IvanCanedo/Re-configurableDrivingSimulatorPrototype/Solidworks/Full-Scale/plataforma.SLDASM

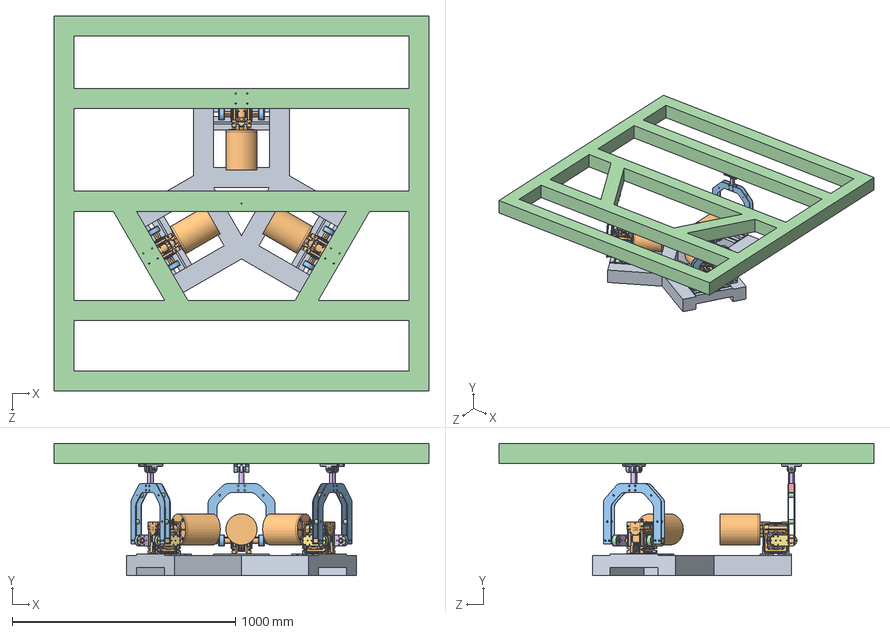
[picture p16: CAD file, 2021-12-05]
Solidworks/Full-Scale/plataforma.SLDASM
1680.0 x 593.5 x 1680.0 mm
base
reductor con motor x 3
cople flecha x 6
cople rodamiento x 6
rodameitno falso x 6
placa manivela x 6
placa manivela 2 x 6
tornillo falso x 72
anillo manivela x 6
pin de manivela x 6
arco x 6
virlo x 12
bloque x 3
rotula x 3
esfera x 3
placa superior x 3
soporte superior x 6
pin superior x 3
virlo superior x 6
base superior
