IvanCanedo/Re-configurableDrivingSimulatorPrototype/Solidworks/Scale/Ensamblaje1.SLDASM

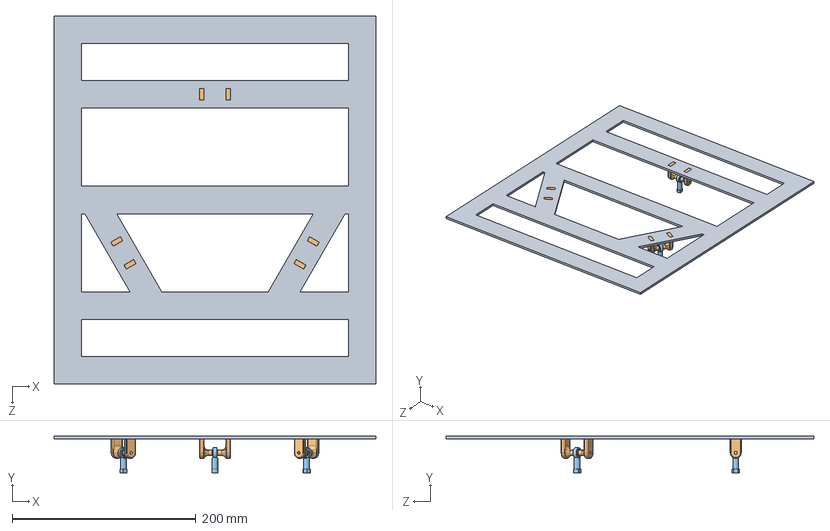
[picture p17: CAD file, 2021-12-05]
Solidworks/Scale/Ensamblaje1.SLDASM
350.0 x 39.7 x 400.0 mm
plataforma superior
soporte superior x 6
rotula de esfera x 3
