IvanCanedo/Re-configurableDrivingSimulatorPrototype/Solidworks/Vehicle control devices/pedalEnsable.SLDASM

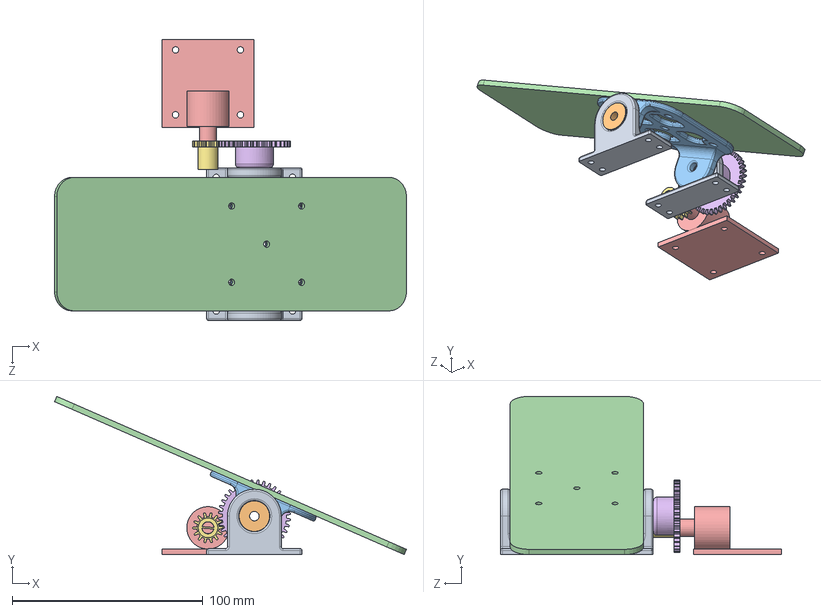
[picture p18: CAD file, 2021-12-05]
Solidworks/Vehicle control devices/pedalEnsable.SLDASM
184.4 x 82.9 x 147.2 mm
abrazadera5-16 x 2
rodamiento5-16 x 2
base pedal
pedal
pot
gear36
gear14
