IvanCanedo/Re-configurableDrivingSimulatorPrototype/Solidworks/Full-Scale/plataforma con perfiles y tornillos.SLDASM

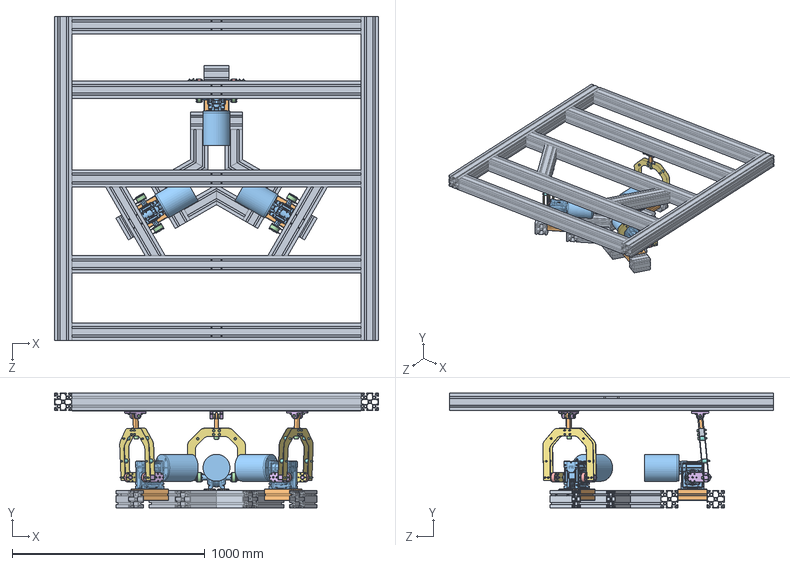
[picture p19: CAD file, 2021-12-05]
Solidworks/Full-Scale/plataforma con perfiles y tornillos.SLDASM
1680.0 x 594.1 x 1680.0 mm
perfil extruido 90x90 x 21
perfil extruido 60x60 x 6
reductor con motor x 3
cople flecha x 6
cople rodamiento x 6
placa manivela 2 x 6
placa manivela x 6
2202_ETN9_3 x 60
2202_ETN9_14 x 60
2202_ETN9_29 x 6
2202_ETN9_31 x 6
socket head cap screw_iso x 129
anillo manivela x 6
pin de manivela x 6
arco x 6
virlo x 12
bloque x 3
rotula x 3
esfera x 3
pin superior x 3
placa superior x 3
soporte superior x 6
virlo superior x 6
