IvanCanedo/Re-configurableDrivingSimulatorPrototype/Solidworks/Full-Scale/soperte superior.SLDASM

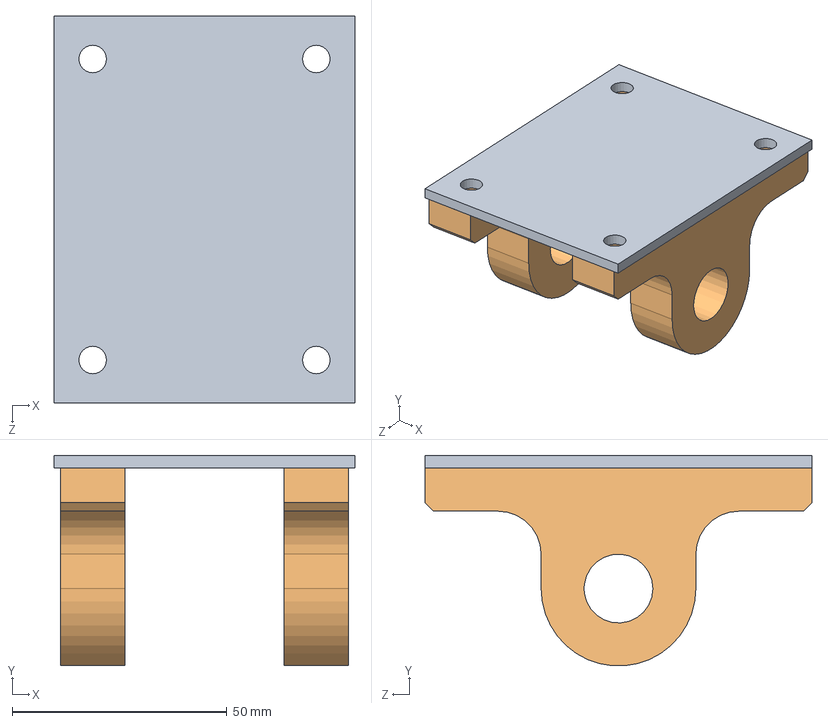
[picture p20: CAD file, 2021-12-05]
Solidworks/Full-Scale/soperte superior.SLDASM
70.0 x 48.9 x 90.0 mm
placa superior
soporte superior x 2
