IvanCanedo/Re-configurableDrivingSimulatorPrototype/Solidworks/Full-Scale/manivela con rodamiento derecha.SLDASM

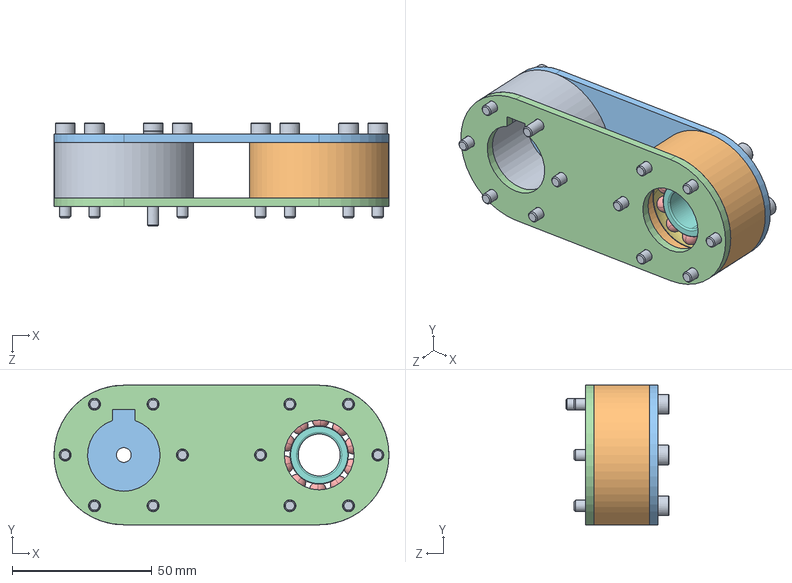
[picture p21: CAD file, 2021-12-05]
Solidworks/Full-Scale/manivela con rodamiento derecha.SLDASM
120.0 x 50.0 x 37.0 mm
cople flecha
cople rodamiento
placa manivela 2
placa manivela
2202_ETN9_3 x 10
2202_ETN9_14 x 10
2202_ETN9_29
2202_ETN9_31
socket head cap screw_iso x 12
anillo manivela
