IvanCanedo/Re-configurableDrivingSimulatorPrototype/Solidworks/Full-Scale/base superior con perfiles.SLDASM

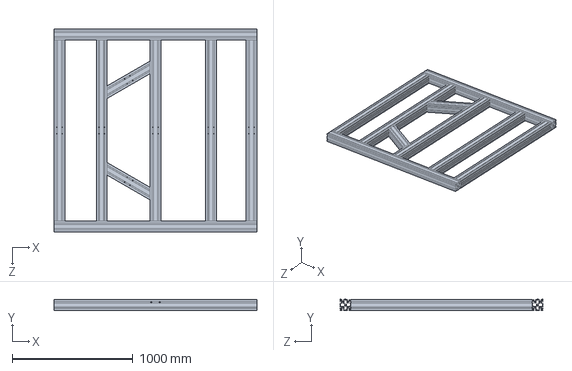
[picture p22: CAD file, 2021-12-05]
Solidworks/Full-Scale/base superior con perfiles.SLDASM
1680.0 x 92.0 x 1680.0 mm
perfil extruido 90x90 x 9
