IvanCanedo/Re-configurableDrivingSimulatorPrototype/Solidworks/Full-Scale/arco ensamble.SLDASM

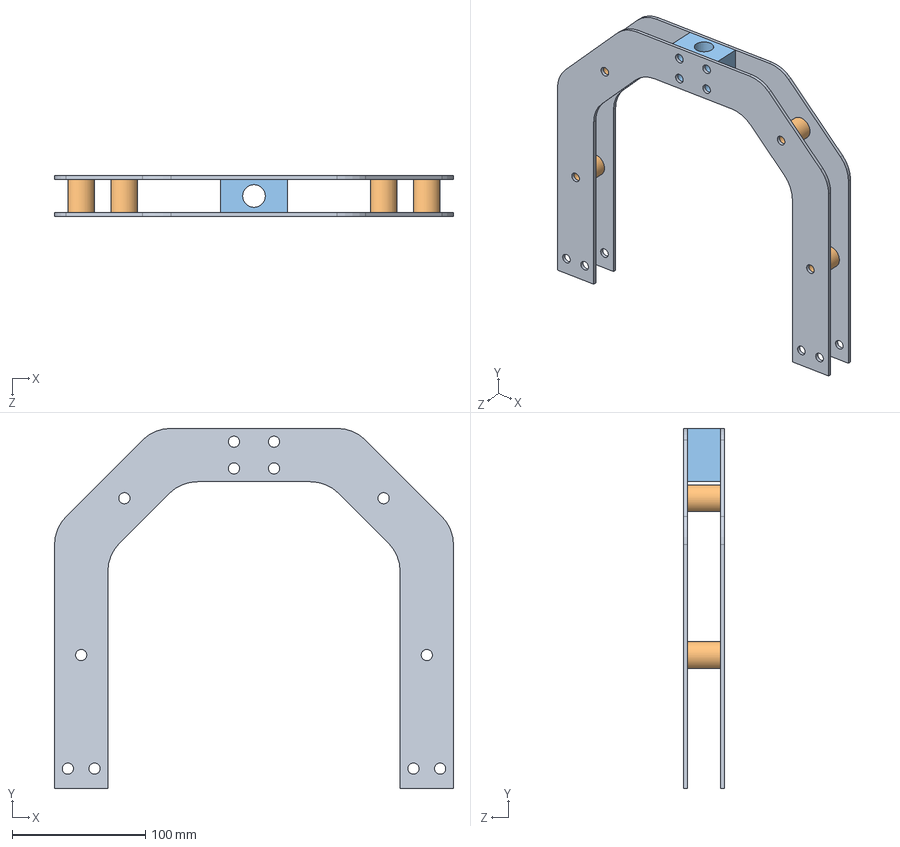
[picture p23: CAD file, 2021-12-05]
Solidworks/Full-Scale/arco ensamble.SLDASM
299.0 x 270.0 x 31.0 mm
arco x 2
virlo x 4
bloque
