IvanCanedo/Re-configurableDrivingSimulatorPrototype/MATLAB/simulacion/pilar.SLDPRT

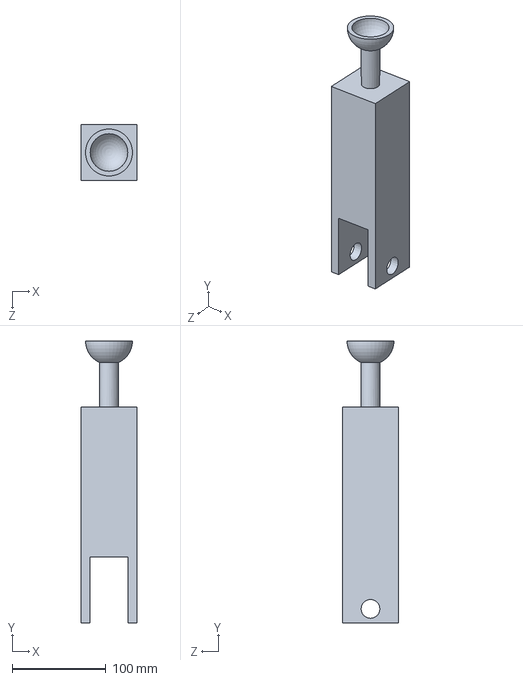
[picture p24: CAD file, 2021-12-05]
MATLAB/simulacion/pilar.SLDPRT
60.0 x 300.0 x 60.0 mm
