IvanCanedo/Re-configurableDrivingSimulatorPrototype/Solidworks/Finite Element/flecha motor.SLDPRT

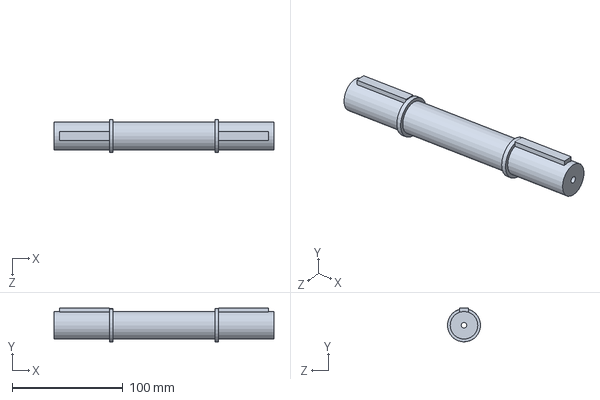
[picture p25: CAD file, 2021-12-05]
Solidworks/Finite Element/flecha motor.SLDPRT
199.0 x 30.5 x 30.0 mm
