IvanCanedo/Re-configurableDrivingSimulatorPrototype/Solidworks/Full-Scale/diagrama base.SLDPRT

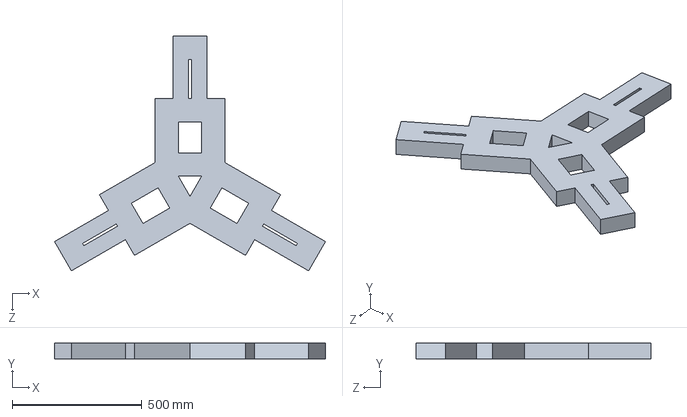
[picture p26: CAD file, 2021-12-05]
Solidworks/Full-Scale/diagrama base.SLDPRT
1043.6 x 60.0 x 903.8 mm
