IvanCanedo/Re-configurableDrivingSimulatorPrototype/Solidworks/Scale/soporte silla.SLDPRT

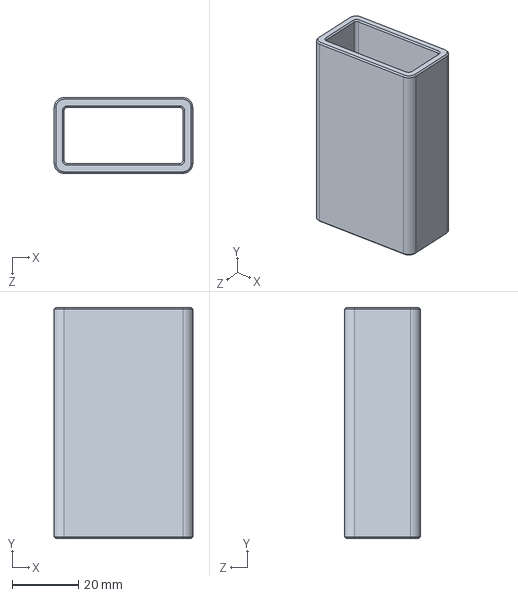
[picture p27: CAD file, 2021-12-05]
Solidworks/Scale/soporte silla.SLDPRT
42.0 x 70.0 x 23.0 mm
