IvanCanedo/Re-configurableDrivingSimulatorPrototype/Solidworks/Vehicle control devices/cople volante.SLDPRT

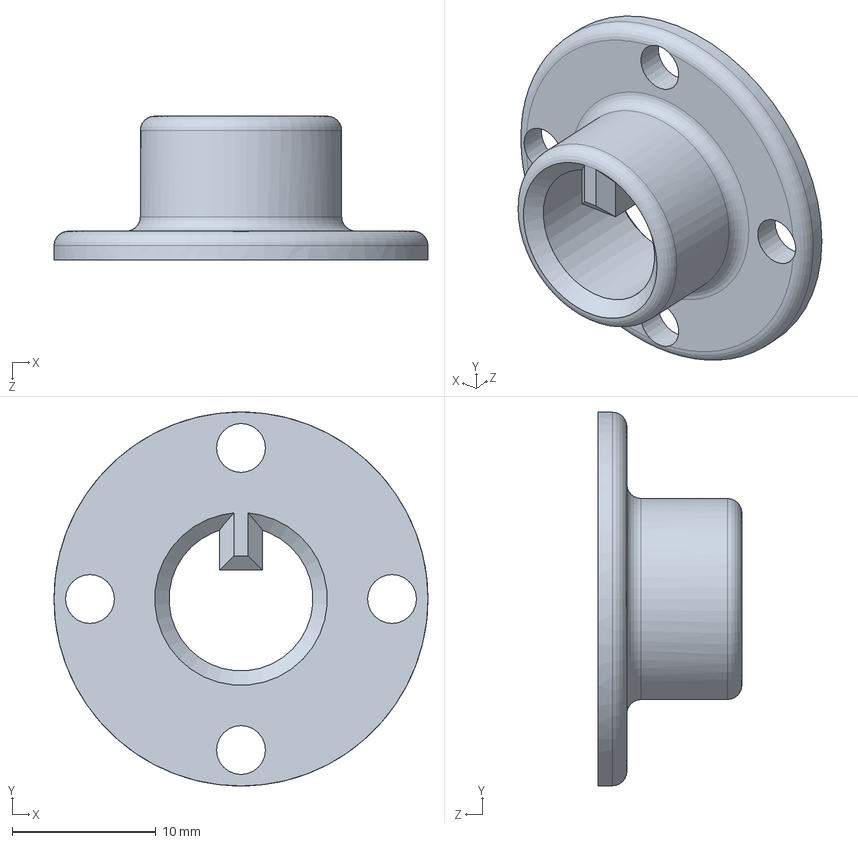
[picture p28: CAD file, 2021-12-05]
Solidworks/Vehicle control devices/cople volante.SLDPRT
26.0 x 26.0 x 10.0 mm
