IvanCanedo/Re-configurableDrivingSimulatorPrototype/Solidworks/Finite Element/bloque.SLDPRT

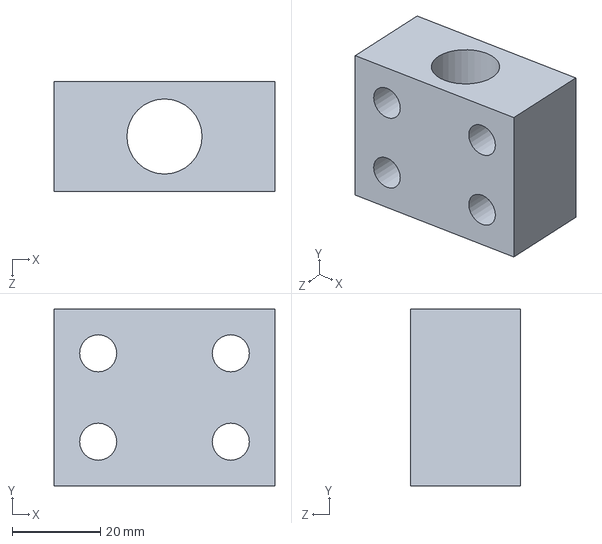
[picture p29: CAD file, 2021-12-05]
Solidworks/Finite Element/bloque.SLDPRT
50.0 x 40.0 x 25.0 mm
