IvanCanedo/Re-configurableDrivingSimulatorPrototype/Solidworks/Full-Scale/cople rodamiento.SLDPRT

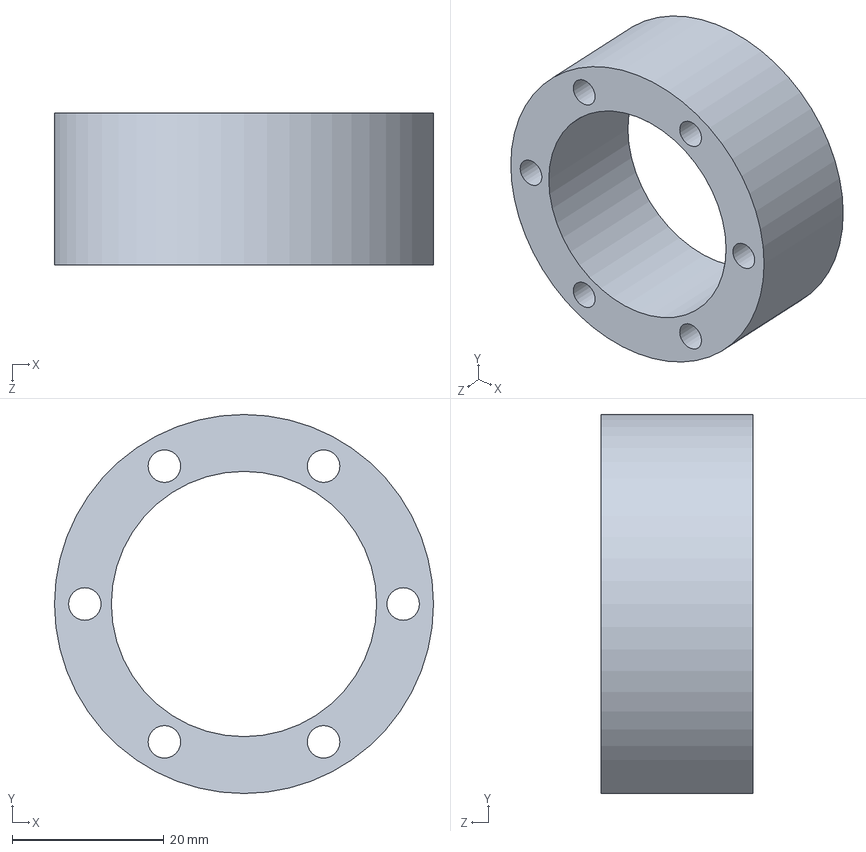
[picture p30: CAD file, 2021-12-05]
Solidworks/Full-Scale/cople rodamiento.SLDPRT
50.0 x 50.0 x 20.0 mm
