IvanCanedo/Re-configurableDrivingSimulatorPrototype/Solidworks/Scale/base plataforma.SLDPRT

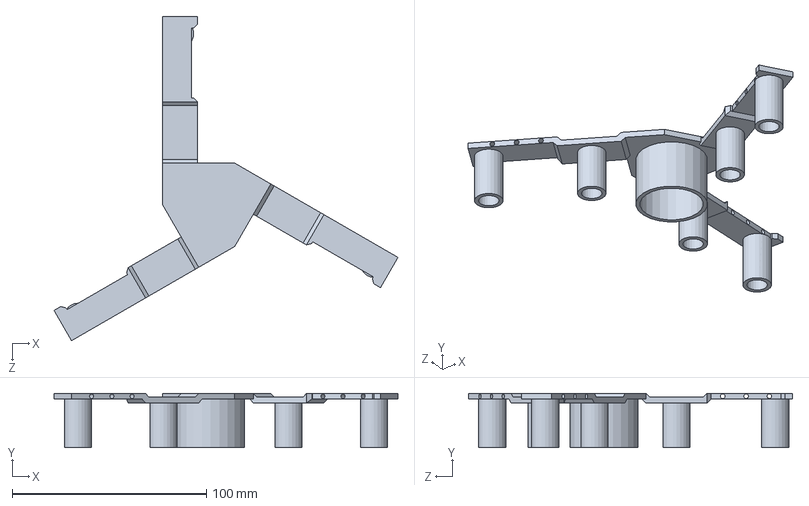
[picture p31: CAD file, 2021-12-05]
Solidworks/Scale/base plataforma.SLDPRT
177.0 x 28.0 x 166.9 mm
