IvanCanedo/Re-configurableDrivingSimulatorPrototype/MATLAB/simulacion/plataforma_Predeterminado_sldprt.STEP

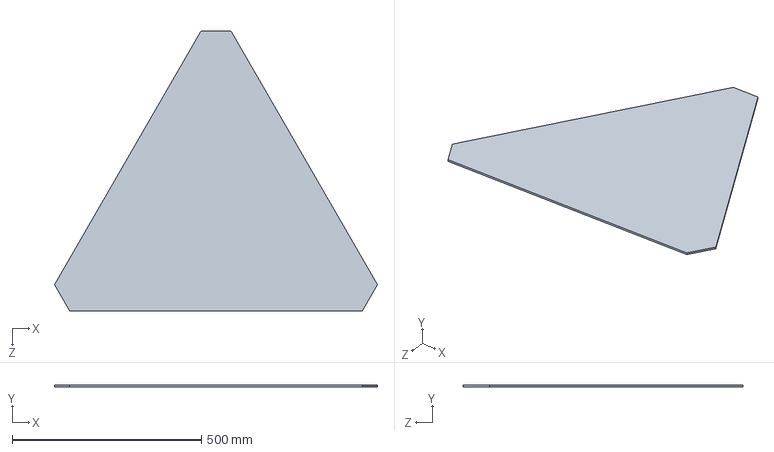
[picture p32: CAD file, 2021-12-05]
MATLAB/simulacion/plataforma_Predeterminado_sldprt.STEP
854.1 x 5.00 x 739.6 mm
