IvanCanedo/Re-configurableDrivingSimulatorPrototype/Solidworks/Finite Element/arco.SLDPRT

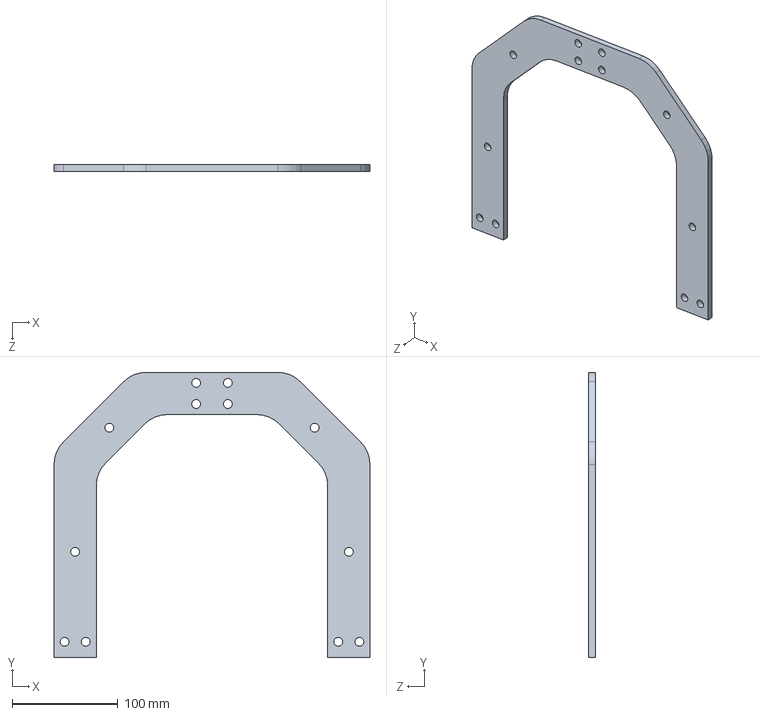
[picture p33: CAD file, 2021-12-05]
Solidworks/Finite Element/arco.SLDPRT
299.0 x 270.0 x 6.35 mm
