IvanCanedo/Re-configurableDrivingSimulatorPrototype/Solidworks/Full-Scale/cople flecha.SLDPRT

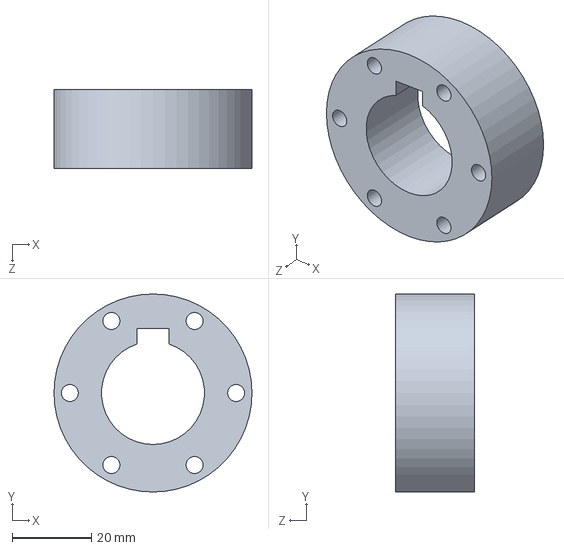
[picture p34: CAD file, 2021-12-05]
Solidworks/Full-Scale/cople flecha.SLDPRT
50.0 x 50.0 x 20.0 mm
