IvanCanedo/Re-configurableDrivingSimulatorPrototype/Solidworks/Scale/soporte superior.SLDPRT

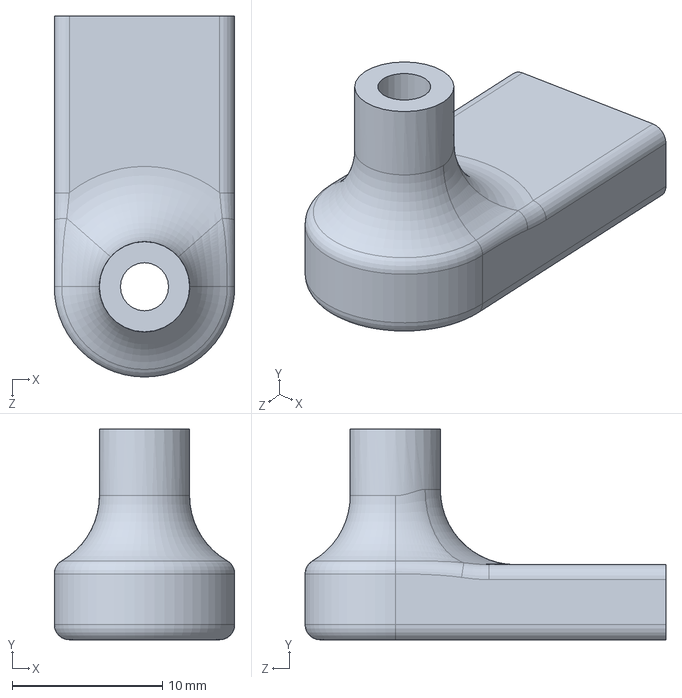
[picture p35: CAD file, 2021-12-05]
Solidworks/Scale/soporte superior.SLDPRT
12.0 x 14.0 x 24.0 mm
