IvanCanedo/Re-configurableDrivingSimulatorPrototype/Solidworks/Vehicle control devices/tapa rodamiento.SLDPRT

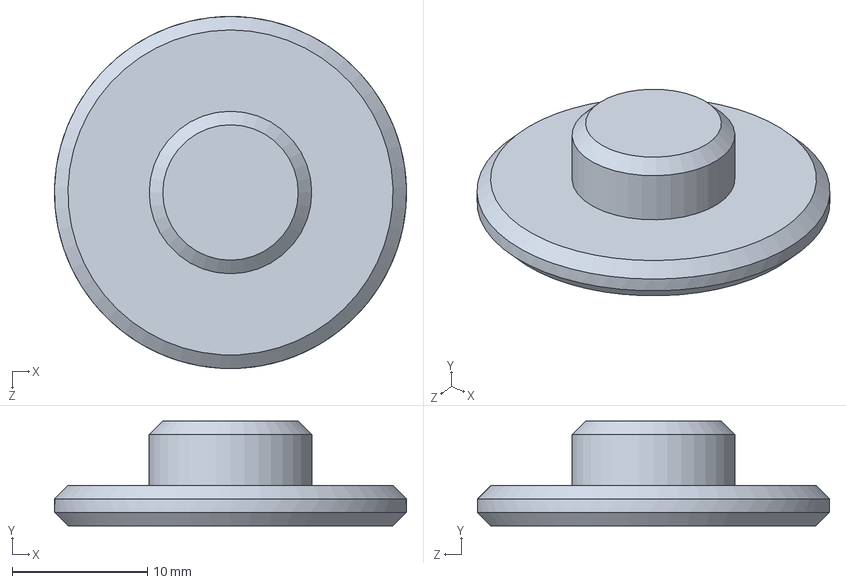
[picture p36: CAD file, 2021-12-05]
Solidworks/Vehicle control devices/tapa rodamiento.SLDPRT
26.0 x 7.75 x 26.0 mm
