IvanCanedo/Re-configurableDrivingSimulatorPrototype/MATLAB/simulacion/plataforma_soporte_Predeterminado_sldprt.STEP

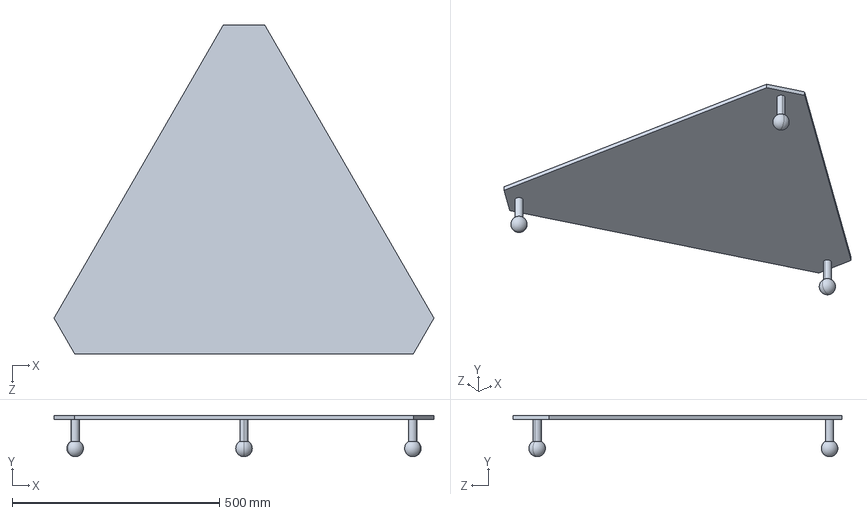
[picture p37: CAD file, 2021-12-05]
MATLAB/simulacion/plataforma_soporte_Predeterminado_sldprt.STEP
916.0 x 100.0 x 793.3 mm
