IvanCanedo/Re-configurableDrivingSimulatorPrototype/Solidworks/Finite Element/esfera.SLDPRT

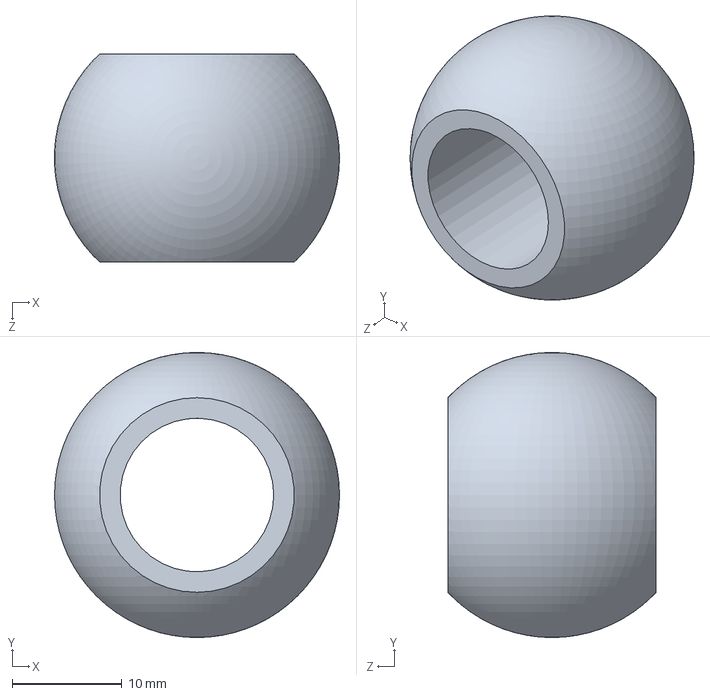
[picture p38: CAD file, 2021-12-05]
Solidworks/Finite Element/esfera.SLDPRT
26.0 x 26.0 x 19.0 mm
