IvanCanedo/Re-configurableDrivingSimulatorPrototype/Solidworks/Scale/rodamiento.SLDPRT

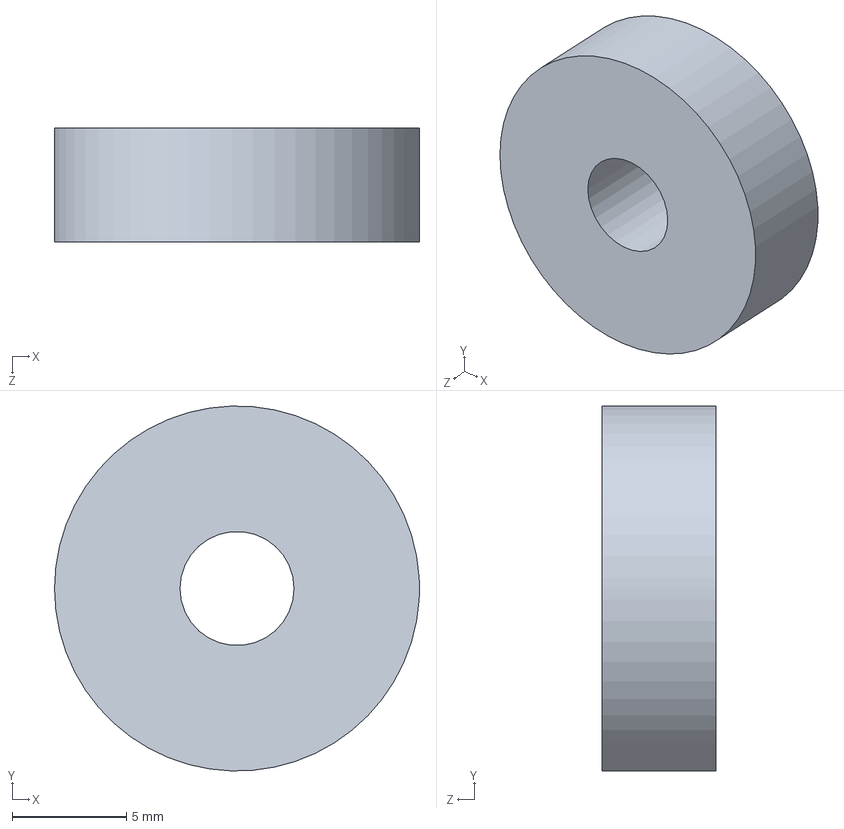
[picture p39: CAD file, 2021-12-05]
Solidworks/Scale/rodamiento.SLDPRT
16.0 x 16.0 x 5.00 mm
