IvanCanedo/Re-configurableDrivingSimulatorPrototype/Solidworks/Vehicle control devices/rodamiento.SLDPRT

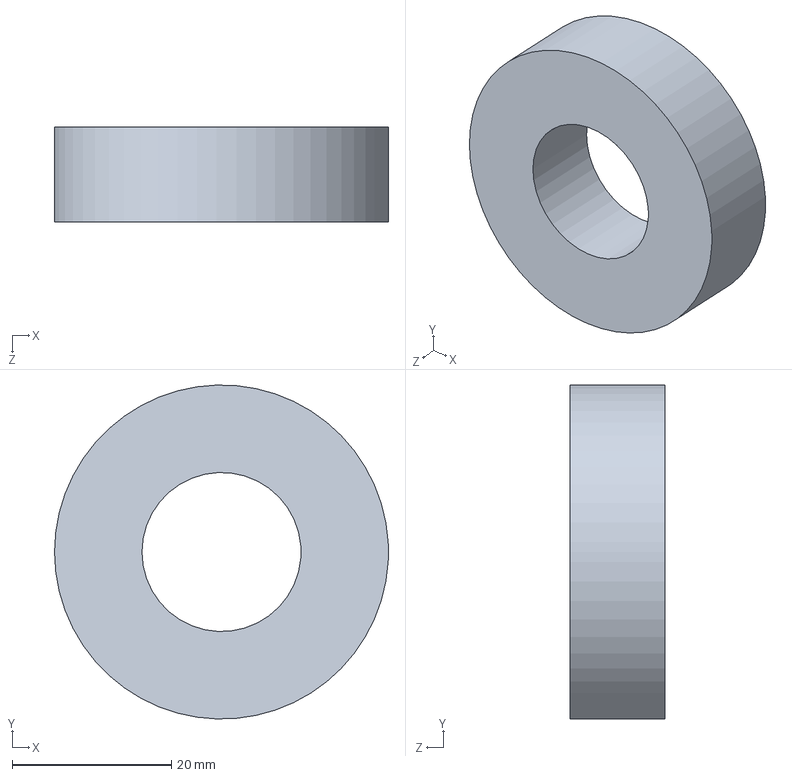
[picture p40: CAD file, 2021-12-05]
Solidworks/Vehicle control devices/rodamiento.SLDPRT
42.0 x 42.0 x 11.9 mm
