IvanCanedo/Re-configurableDrivingSimulatorPrototype/MATLAB/simulacion/pin inferior.SLDPRT

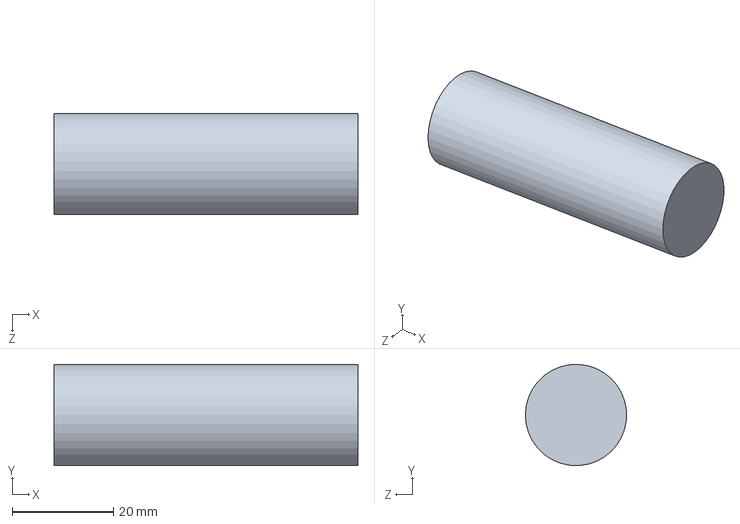
[picture p41: CAD file, 2021-12-05]
MATLAB/simulacion/pin inferior.SLDPRT
60.0 x 20.0 x 20.0 mm
