IvanCanedo/Re-configurableDrivingSimulatorPrototype/Solidworks/Scale/puente.SLDPRT

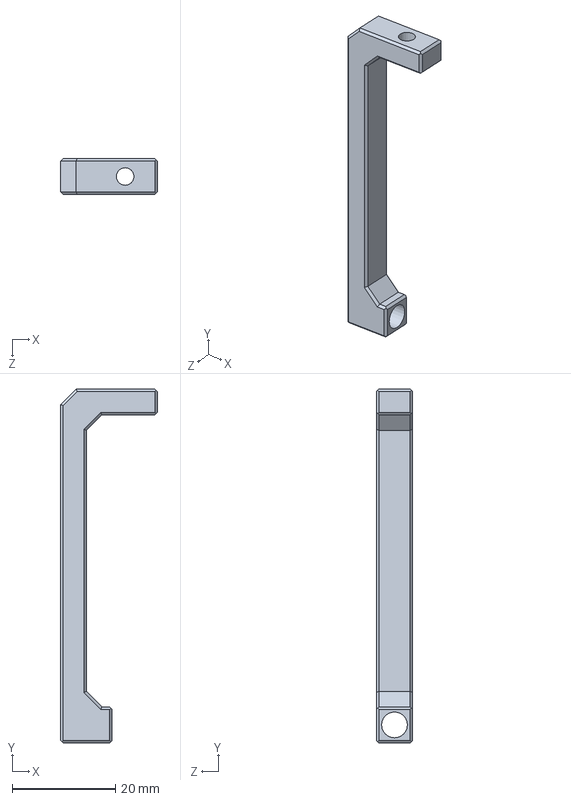
[picture p42: CAD file, 2021-12-05]
Solidworks/Scale/puente.SLDPRT
18.8 x 68.5 x 7.00 mm
