IvanCanedo/Re-configurableDrivingSimulatorPrototype/Solidworks/Vehicle control devices/abrazadera5-16.SLDPRT

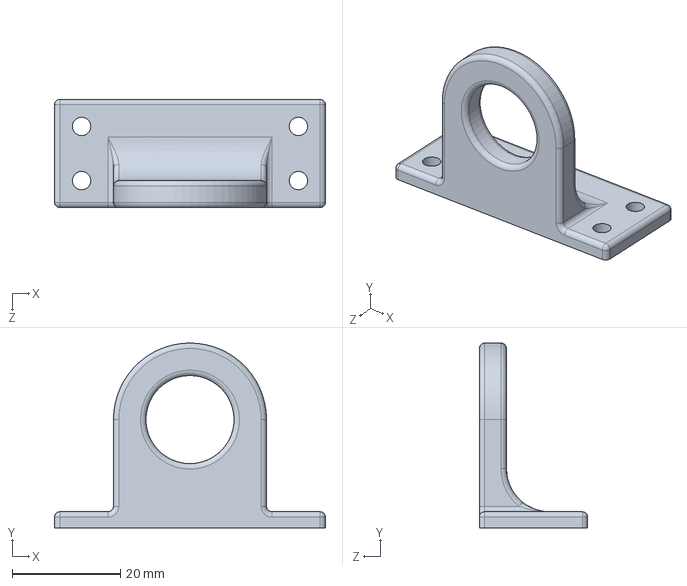
[picture p43: CAD file, 2021-12-05]
Solidworks/Vehicle control devices/abrazadera5-16.SLDPRT
50.0 x 34.1 x 20.0 mm
