IvanCanedo/Re-configurableDrivingSimulatorPrototype/Solidworks/Vehicle control devices/base pedal.SLDPRT

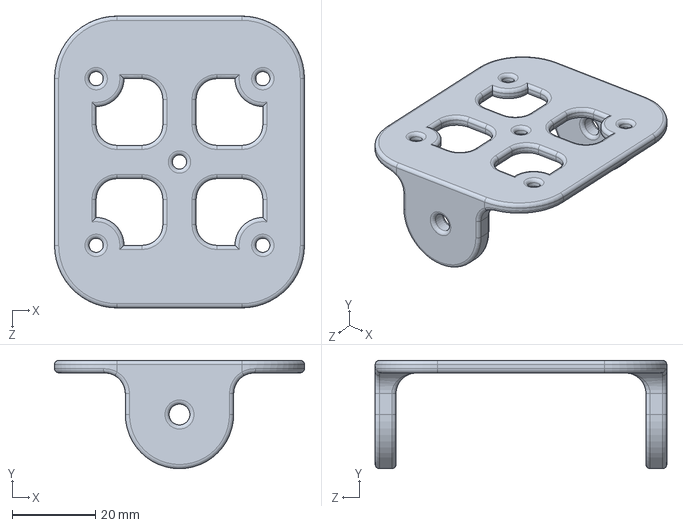
[picture p44: CAD file, 2021-12-05]
Solidworks/Vehicle control devices/base pedal.SLDPRT
60.0 x 26.0 x 70.0 mm
