IvanCanedo/Re-configurableDrivingSimulatorPrototype/MATLAB/simulacion/viela_Predeterminado_sldprt.STEP

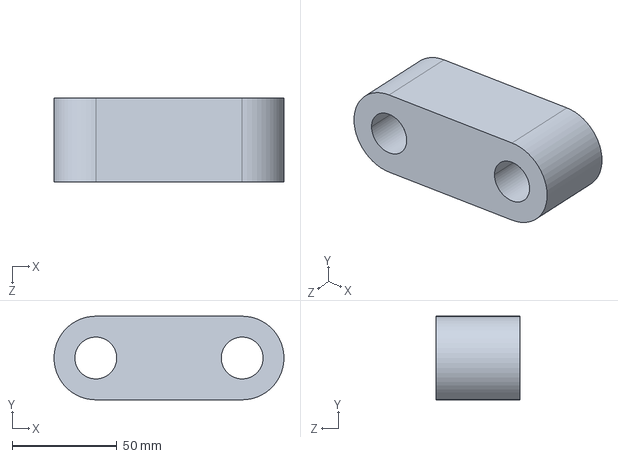
[picture p45: CAD file, 2021-12-05]
MATLAB/simulacion/viela_Predeterminado_sldprt.STEP
110.0 x 40.0 x 40.0 mm
