IvanCanedo/Re-configurableDrivingSimulatorPrototype/Solidworks/Full-Scale/placa manivela.SLDPRT

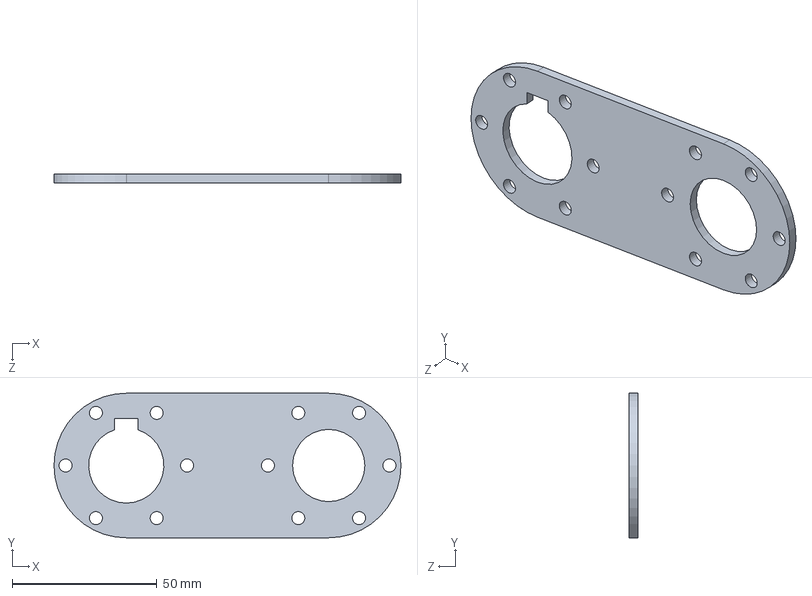
[picture p46: CAD file, 2021-12-05]
Solidworks/Full-Scale/placa manivela.SLDPRT
120.0 x 50.0 x 3.00 mm
