IvanCanedo/Re-configurableDrivingSimulatorPrototype/Solidworks/Finite Element/base superior.SLDPRT

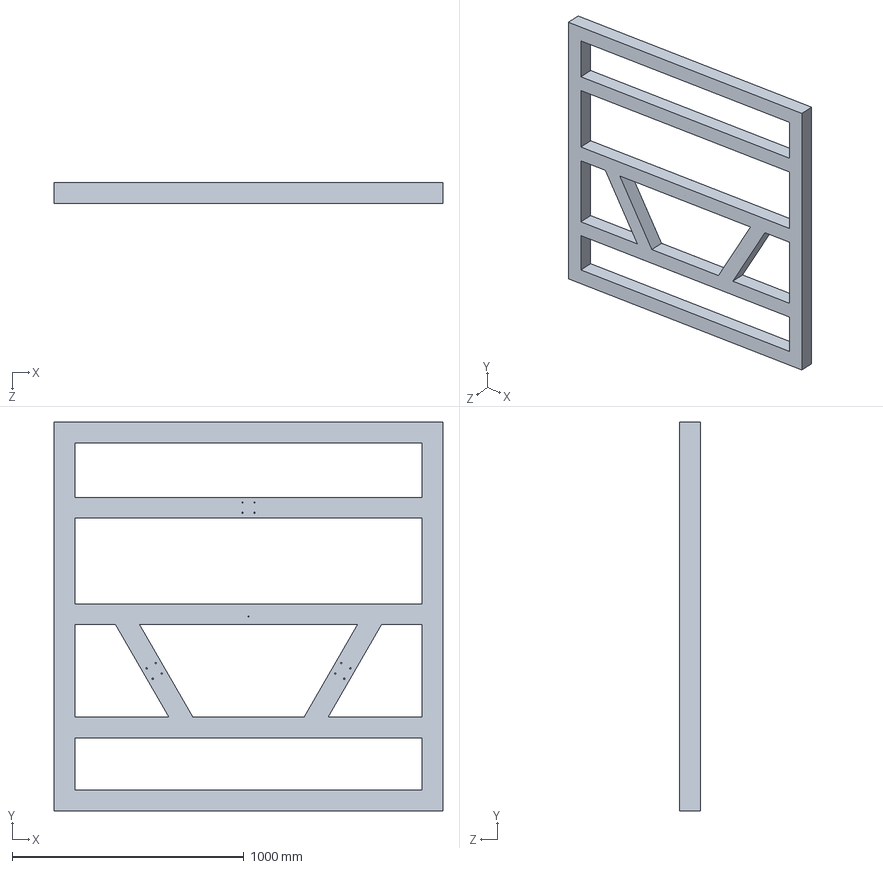
[picture p47: CAD file, 2021-12-05]
Solidworks/Finite Element/base superior.SLDPRT
1680.0 x 1680.0 x 90.0 mm
