IvanCanedo/Re-configurableDrivingSimulatorPrototype/Solidworks/Full-Scale/esfera.SLDPRT

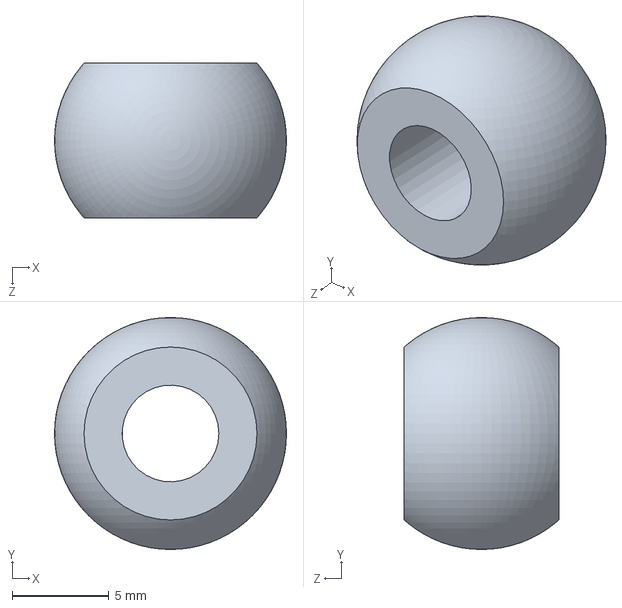
[picture p48: CAD file, 2021-12-05]
Solidworks/Full-Scale/esfera.SLDPRT
12.0 x 12.0 x 8.00 mm
