IvanCanedo/Re-configurableDrivingSimulatorPrototype/Solidworks/Scale/plataforma superior.SLDPRT

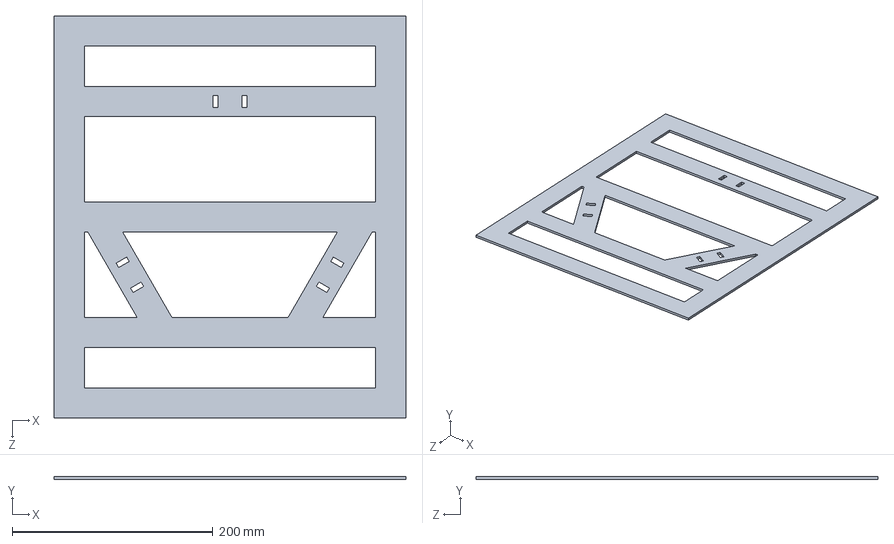
[picture p49: CAD file, 2021-12-05]
Solidworks/Scale/plataforma superior.SLDPRT
350.0 x 3.00 x 400.0 mm
