IvanCanedo/Re-configurableDrivingSimulatorPrototype/Solidworks/Vehicle control devices/pedal.SLDPRT

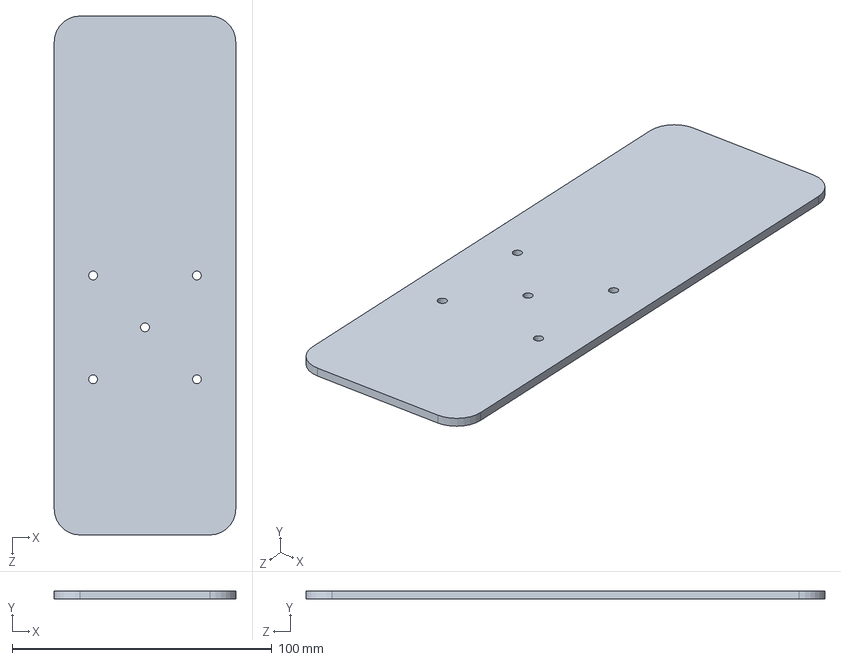
[picture p50: CAD file, 2021-12-05]
Solidworks/Vehicle control devices/pedal.SLDPRT
70.0 x 3.00 x 200.0 mm
