IvanCanedo/Re-configurableDrivingSimulatorPrototype/MATLAB/simulacion/soporte sup_Predeterminado_sldprt.STEP

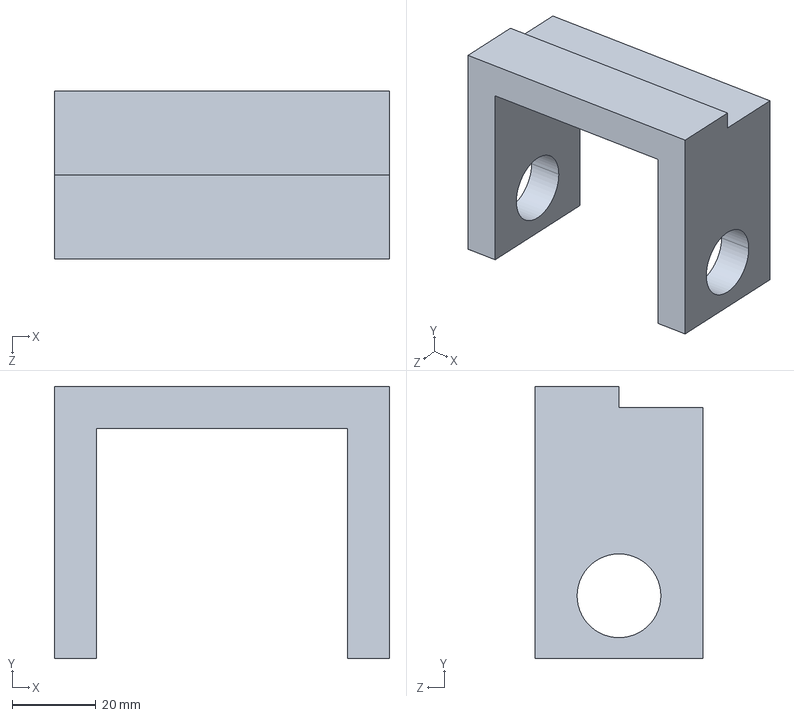
[picture p51: CAD file, 2021-12-05]
MATLAB/simulacion/soporte sup_Predeterminado_sldprt.STEP
80.0 x 65.0 x 40.0 mm
