IvanCanedo/Re-configurableDrivingSimulatorPrototype/Solidworks/Finite Element/anillo manivela.SLDPRT

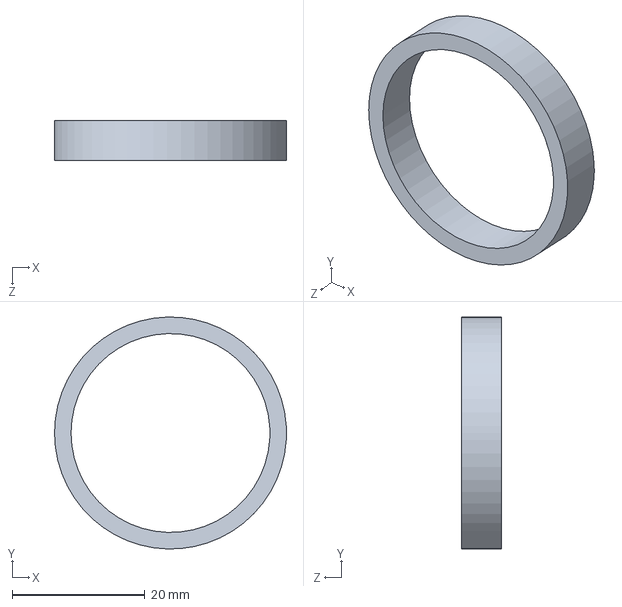
[picture p52: CAD file, 2021-12-05]
Solidworks/Finite Element/anillo manivela.SLDPRT
35.0 x 35.0 x 6.00 mm
