IvanCanedo/Re-configurableDrivingSimulatorPrototype/Solidworks/Scale/manivela.SLDPRT

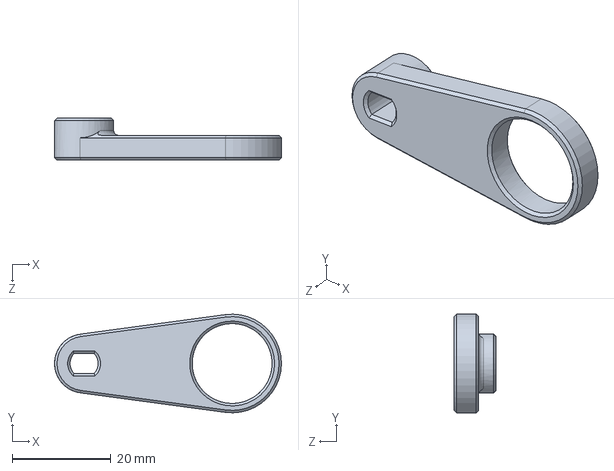
[picture p53: CAD file, 2021-12-05]
Solidworks/Scale/manivela.SLDPRT
46.0 x 20.0 x 8.50 mm
