IvanCanedo/Re-configurableDrivingSimulatorPrototype/Solidworks/Vehicle control devices/gear36-recovered.step

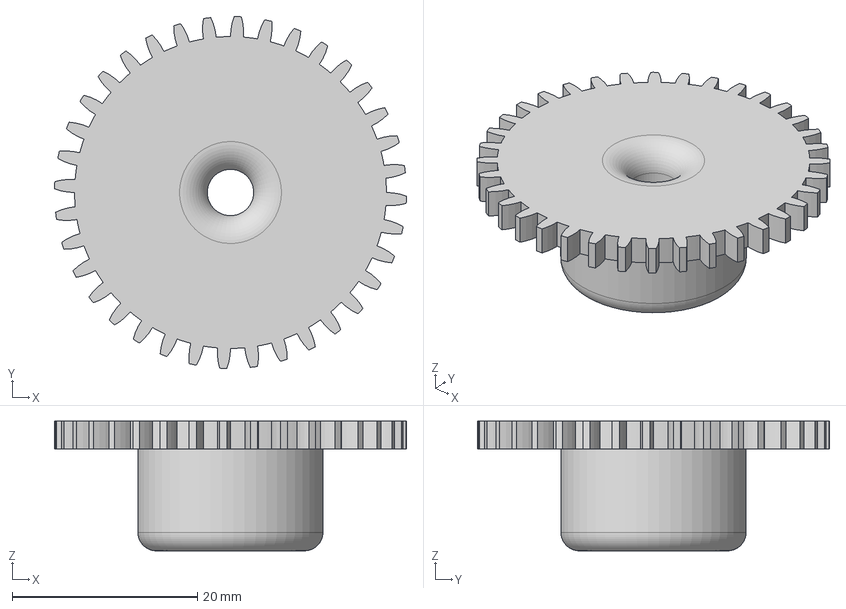
[picture p54: CAD file, 2021-12-05]
Solidworks/Vehicle control devices/gear36-recovered.step
38.0 x 38.0 x 14.0 mm
