IvanCanedo/Re-configurableDrivingSimulatorPrototype/MATLAB/simulacion/base.SLDPRT

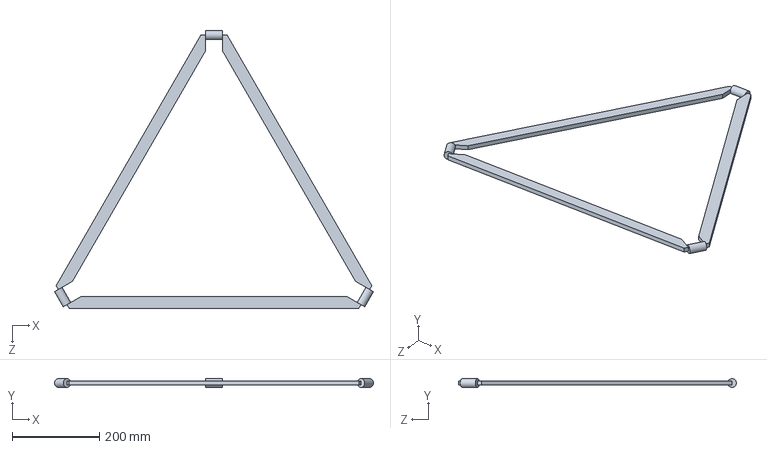
[picture p55: CAD file, 2021-12-05]
MATLAB/simulacion/base.SLDPRT
730.1 x 20.0 x 636.0 mm
