IvanCanedo/Re-configurableDrivingSimulatorPrototype/Solidworks/Scale/puente2.SLDPRT

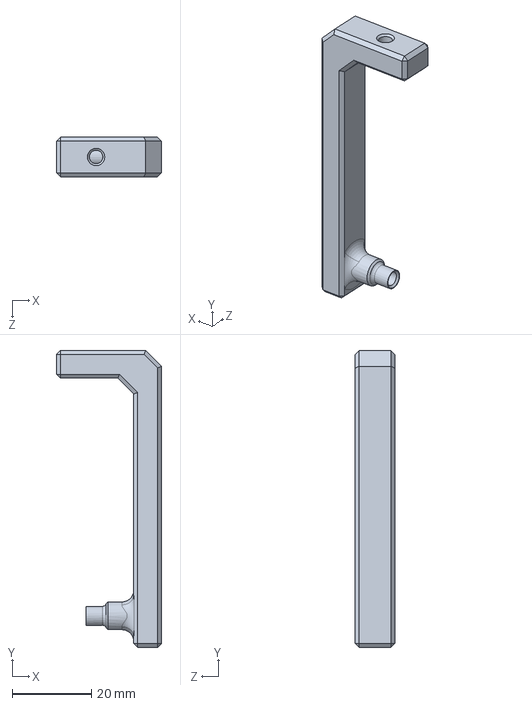
[picture p56: CAD file, 2021-12-05]
Solidworks/Scale/puente2.SLDPRT
26.5 x 75.0 x 10.0 mm
