IvanCanedo/Re-configurableDrivingSimulatorPrototype/MATLAB/simulacion/viela2.SLDPRT

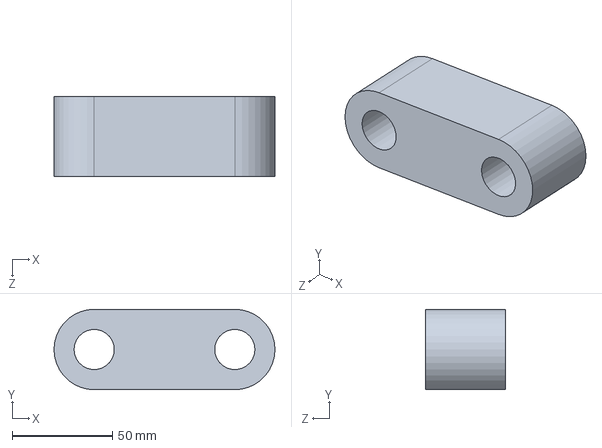
[picture p57: CAD file, 2021-12-05]
MATLAB/simulacion/viela2.SLDPRT
110.0 x 40.0 x 40.0 mm
