IvanCanedo/Re-configurableDrivingSimulatorPrototype/Solidworks/Full-Scale/perfil extruido 90x90.SLDPRT

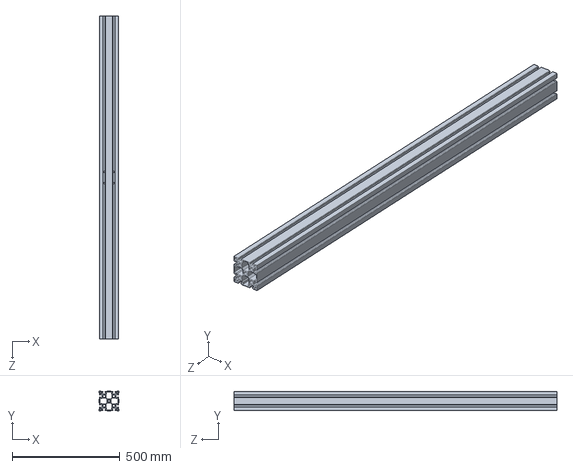
[picture p58: CAD file, 2021-12-05]
Solidworks/Full-Scale/perfil extruido 90x90.SLDPRT
90.0 x 90.0 x 1500.0 mm
