IvanCanedo/Re-configurableDrivingSimulatorPrototype/Solidworks/Scale/rotula de esfera.SLDPRT

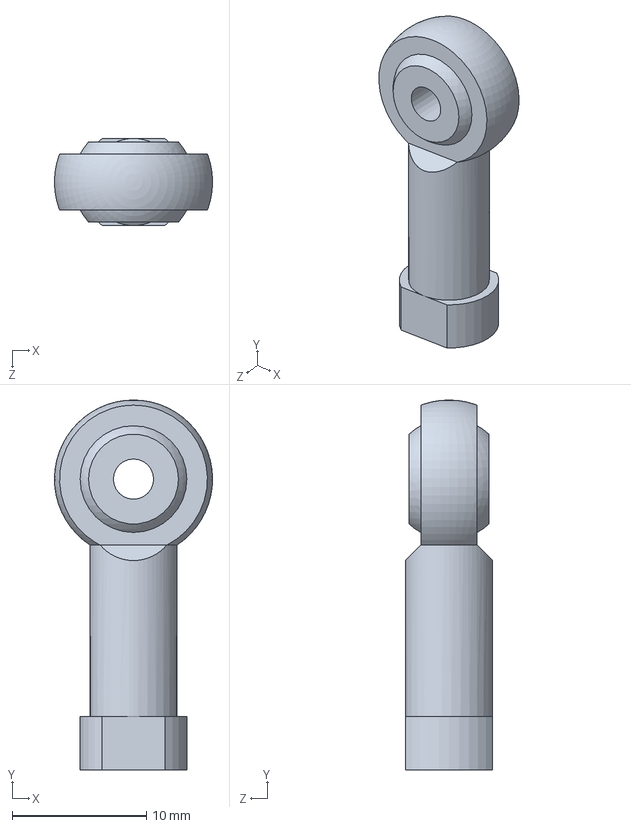
[picture p59: CAD file, 2021-12-05]
Solidworks/Scale/rotula de esfera.SLDPRT
11.8 x 27.6 x 6.50 mm
