IvanCanedo/Re-configurableDrivingSimulatorPrototype/Solidworks/Vehicle control devices/eje.SLDPRT

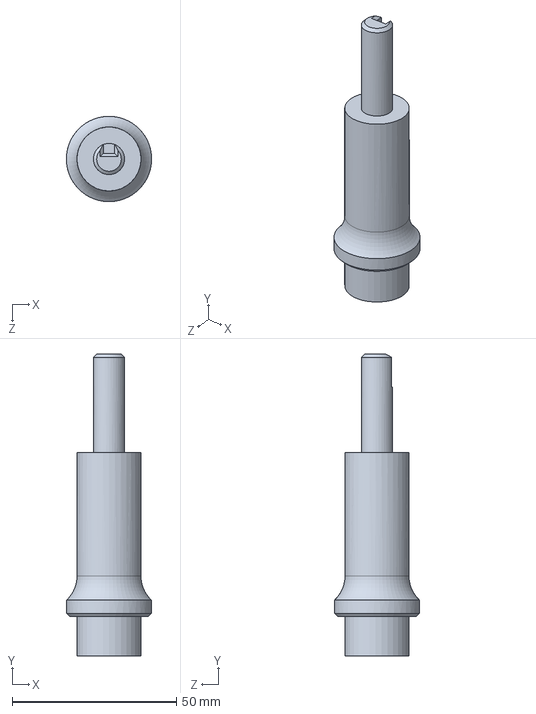
[picture p60: CAD file, 2021-12-05]
Solidworks/Vehicle control devices/eje.SLDPRT
26.0 x 92.0 x 26.0 mm
