IvanCanedo/Re-configurableDrivingSimulatorPrototype/Solidworks/Scale/tapa rodamiento.SLDPRT

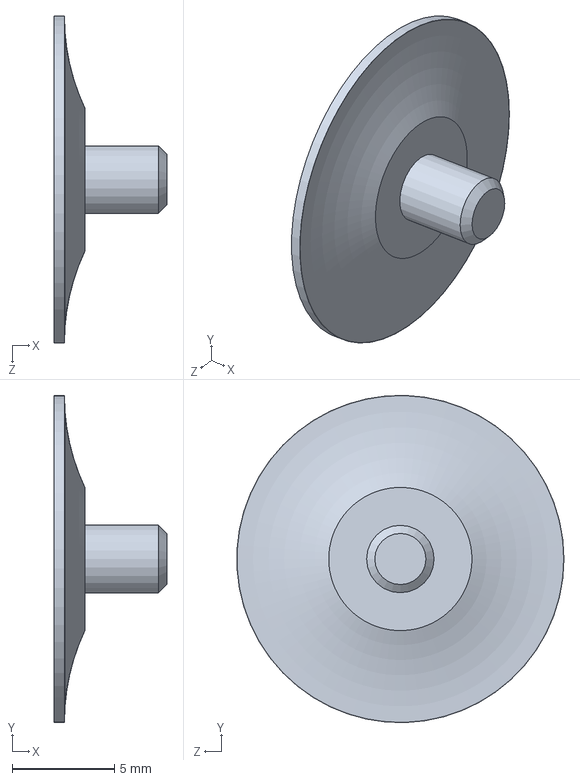
[picture p61: CAD file, 2021-12-05]
Solidworks/Scale/tapa rodamiento.SLDPRT
5.50 x 16.0 x 16.0 mm
