IvanCanedo/Re-configurableDrivingSimulatorPrototype/Solidworks/Vehicle control devices/abrazadera.SLDPRT

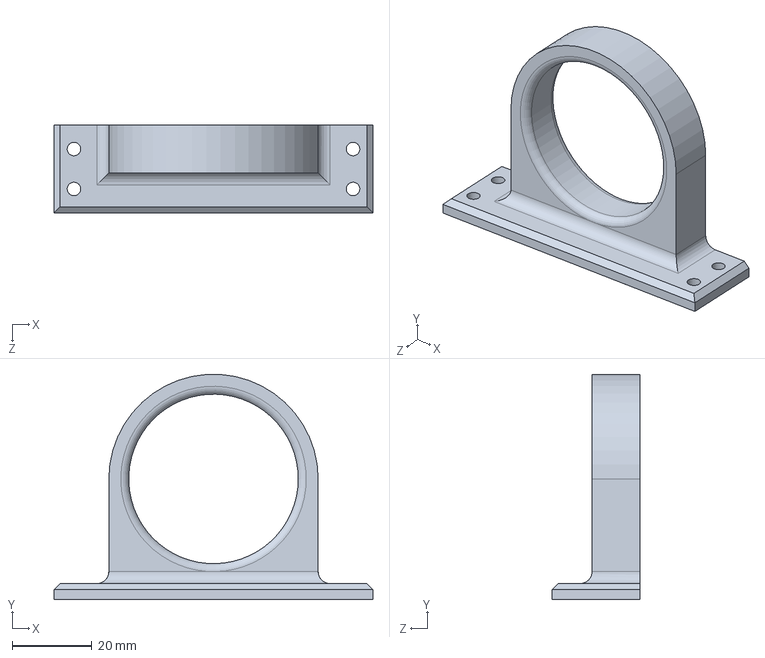
[picture p62: CAD file, 2021-12-05]
Solidworks/Vehicle control devices/abrazadera.SLDPRT
80.0 x 56.4 x 22.0 mm
