IvanCanedo/Re-configurableDrivingSimulatorPrototype/Solidworks/Full-Scale/placa manivela 2.SLDPRT

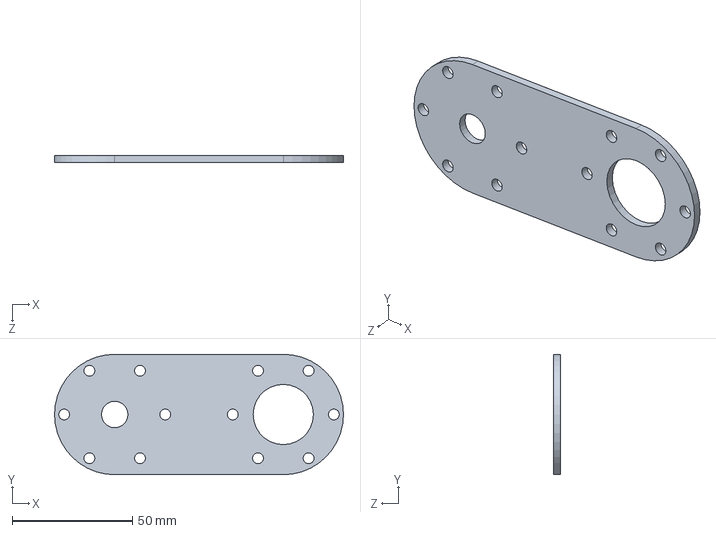
[picture p63: CAD file, 2021-12-05]
Solidworks/Full-Scale/placa manivela 2.SLDPRT
120.0 x 50.0 x 3.00 mm
