IvanCanedo/Re-configurableDrivingSimulatorPrototype/Solidworks/Scale/base motor.SLDPRT

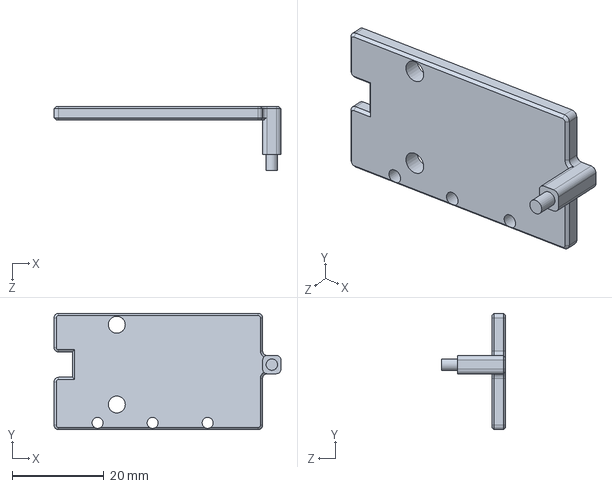
[picture p64: CAD file, 2021-12-05]
Solidworks/Scale/base motor.SLDPRT
49.5 x 25.4 x 14.0 mm
