IvanCanedo/Re-configurableDrivingSimulatorPrototype/Solidworks/Vehicle control devices/gear14.step

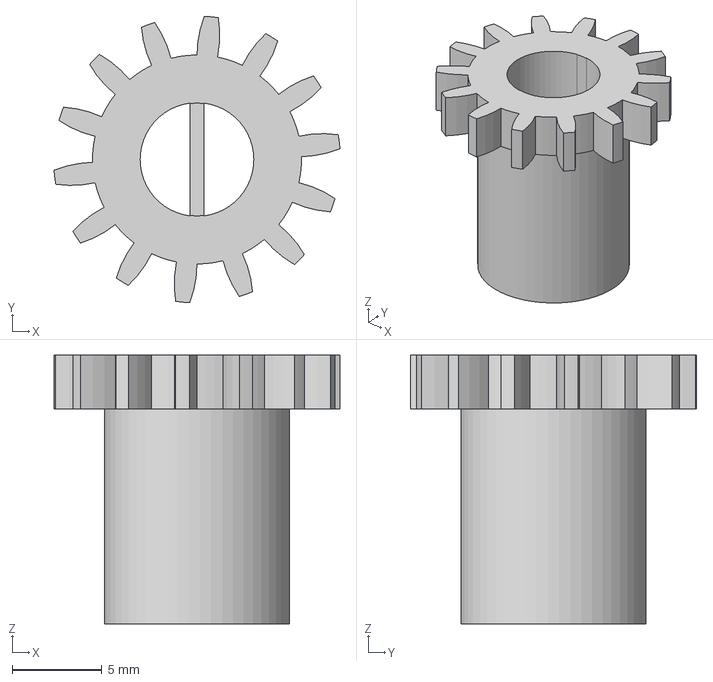
[picture p65: CAD file, 2021-12-05]
Solidworks/Vehicle control devices/gear14.step
16.0 x 16.0 x 15.0 mm
