IvanCanedo/Re-configurableDrivingSimulatorPrototype/Solidworks/Full-Scale/rotula.SLDPRT

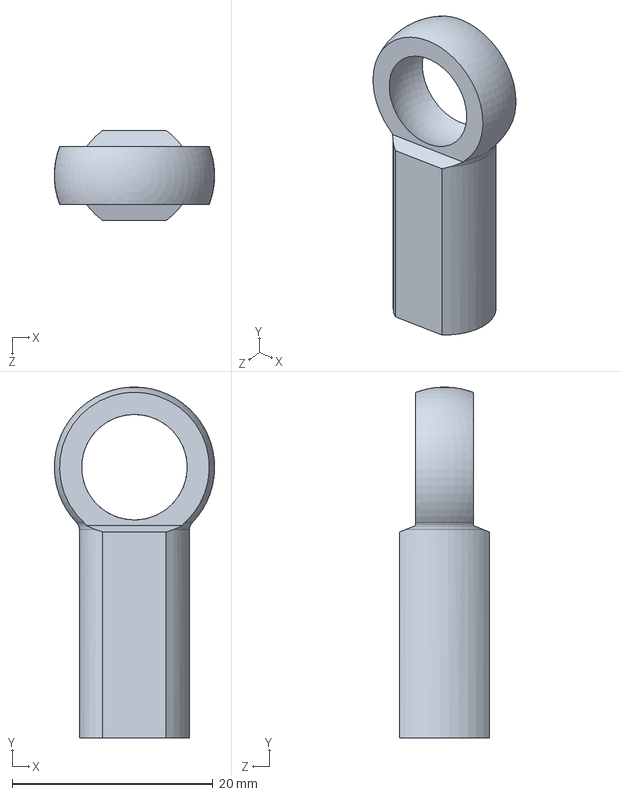
[picture p66: CAD file, 2021-12-05]
Solidworks/Full-Scale/rotula.SLDPRT
16.0 x 35.0 x 9.00 mm
