IvanCanedo/Re-configurableDrivingSimulatorPrototype/Solidworks/Scale/motor.SLDPRT

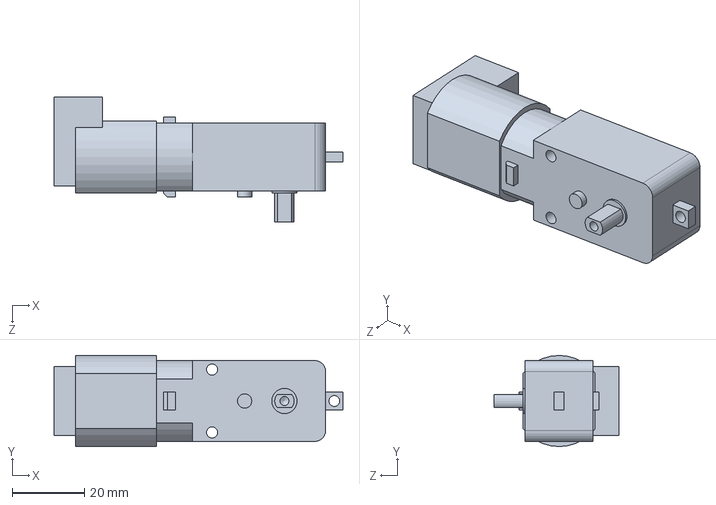
[picture p67: CAD file, 2021-12-05]
Solidworks/Scale/motor.SLDPRT
79.9 x 25.2 x 34.6 mm
