IvanCanedo/Re-configurableDrivingSimulatorPrototype/Solidworks/Vehicle control devices/SteeringWheel.SLDPRT

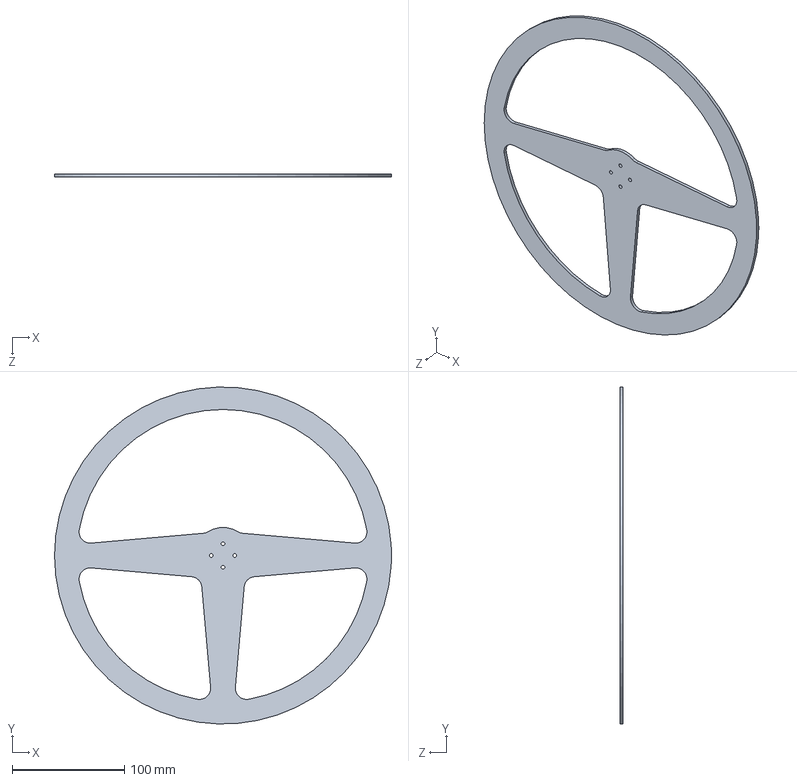
[picture p68: CAD file, 2021-12-05]
Solidworks/Vehicle control devices/SteeringWheel.SLDPRT
300.0 x 299.9 x 3.00 mm
