IvanCanedo/Re-configurableDrivingSimulatorPrototype/Solidworks/Vehicle control devices/pot.SLDPRT

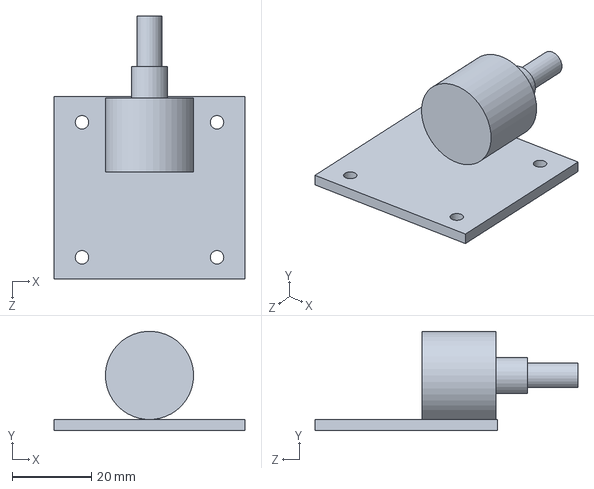
[picture p69: CAD file, 2021-12-05]
Solidworks/Vehicle control devices/pot.SLDPRT
48.0 x 25.0 x 66.2 mm
