IvanCanedo/Re-configurableDrivingSimulatorPrototype/Solidworks/Full-Scale/virlo.SLDPRT

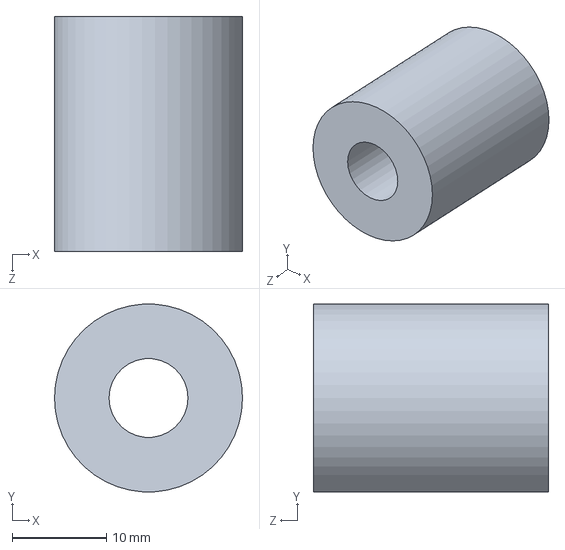
[picture p70: CAD file, 2021-12-05]
Solidworks/Full-Scale/virlo.SLDPRT
20.0 x 20.0 x 25.0 mm
