IvanCanedo/Re-configurableDrivingSimulatorPrototype/Solidworks/Vehicle control devices/tapa.SLDPRT

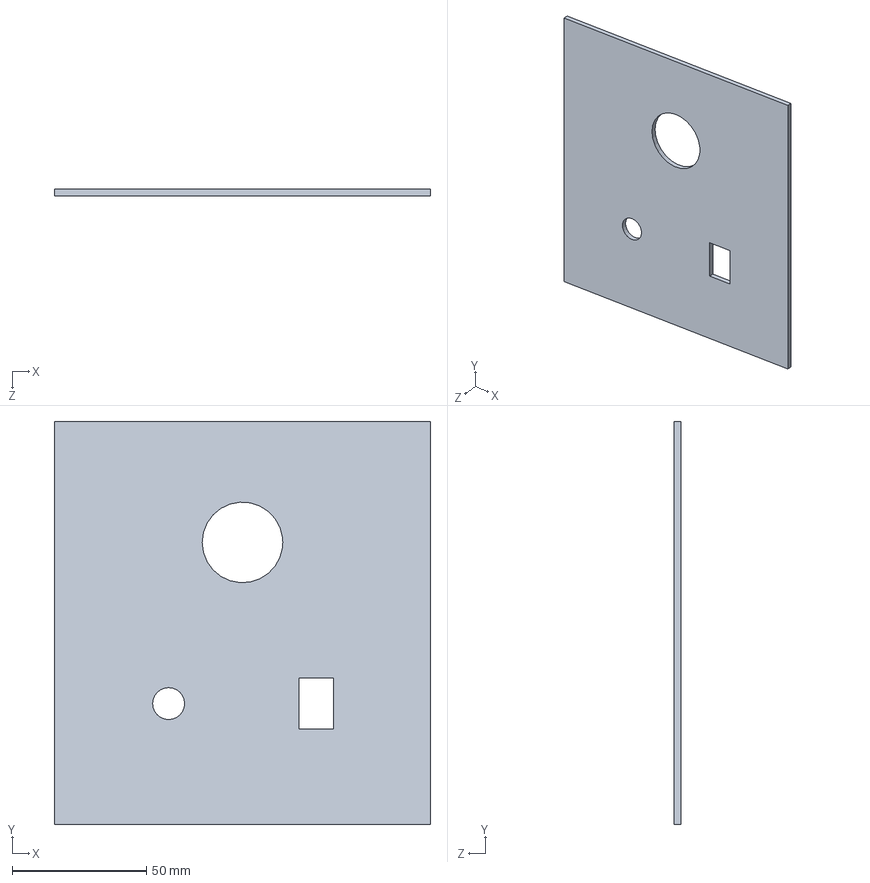
[picture p71: CAD file, 2021-12-05]
Solidworks/Vehicle control devices/tapa.SLDPRT
140.0 x 150.0 x 2.50 mm
