IvanCanedo/Re-configurableDrivingSimulatorPrototype/Solidworks/Full-Scale/placa superior.SLDPRT

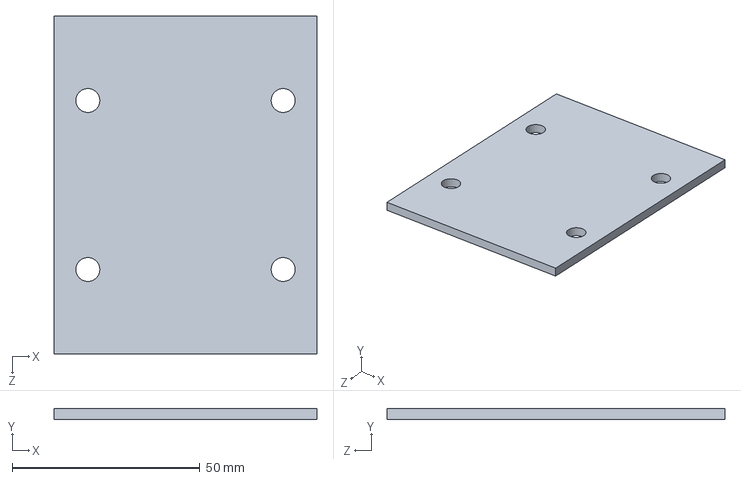
[picture p72: CAD file, 2021-12-05]
Solidworks/Full-Scale/placa superior.SLDPRT
70.0 x 3.00 x 90.0 mm
