IvanCanedo/Re-configurableDrivingSimulatorPrototype/Solidworks/Full-Scale/perfil extruido 60x60.SLDPRT

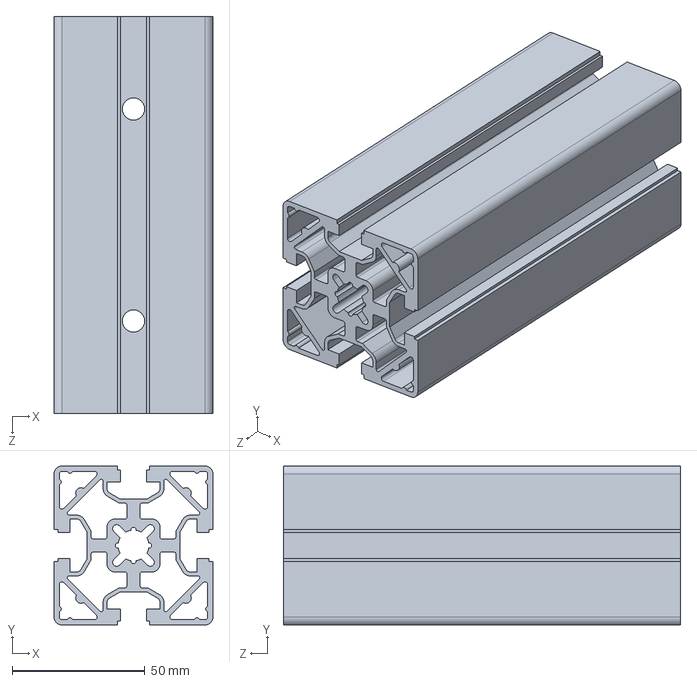
[picture p73: CAD file, 2021-12-05]
Solidworks/Full-Scale/perfil extruido 60x60.SLDPRT
60.0 x 60.0 x 150.0 mm
