IvanCanedo/Re-configurableDrivingSimulatorPrototype/Solidworks/Full-Scale/rodameitno falso.SLDPRT

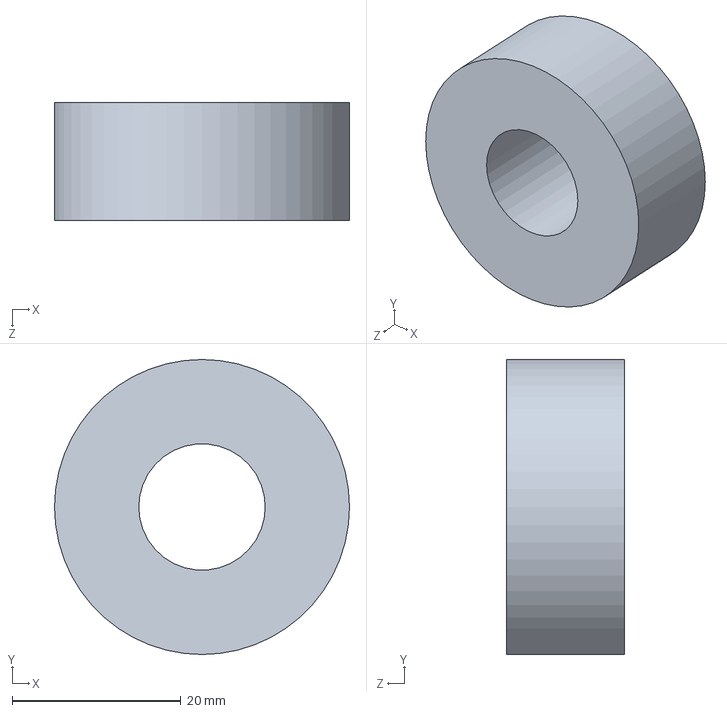
[picture p74: CAD file, 2021-12-05]
Solidworks/Full-Scale/rodameitno falso.SLDPRT
35.0 x 35.0 x 14.0 mm
