IvanCanedo/Re-configurableDrivingSimulatorPrototype/Solidworks/Full-Scale/soporte superior.SLDPRT

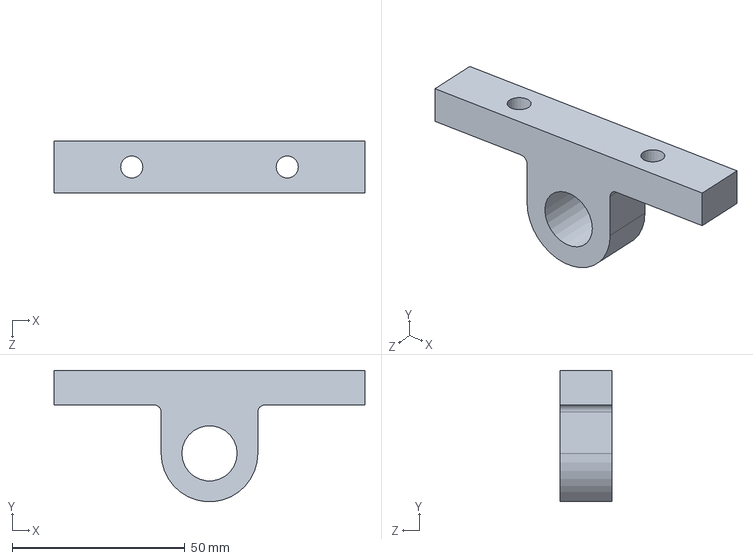
[picture p75: CAD file, 2021-12-05]
Solidworks/Full-Scale/soporte superior.SLDPRT
90.0 x 37.9 x 15.0 mm
