IvanCanedo/Re-configurableDrivingSimulatorPrototype/Solidworks/Full-Scale/tornillo falso.SLDPRT

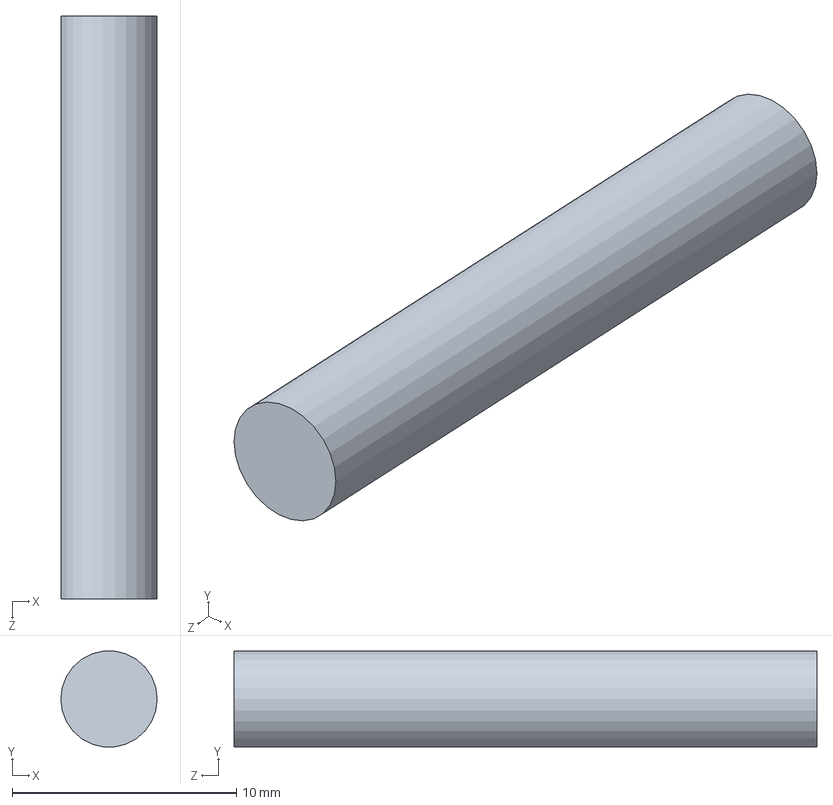
[picture p76: CAD file, 2021-12-05]
Solidworks/Full-Scale/tornillo falso.SLDPRT
4.30 x 4.27 x 26.0 mm
