IvanCanedo/Re-configurableDrivingSimulatorPrototype/Solidworks/Full-Scale/pin de manivela.SLDPRT

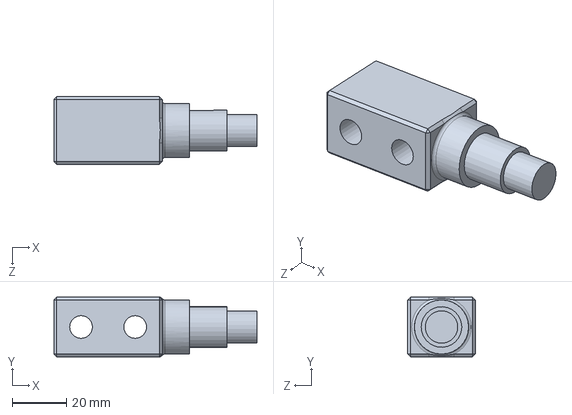
[picture p77: CAD file, 2021-12-05]
Solidworks/Full-Scale/pin de manivela.SLDPRT
75.0 x 22.0 x 25.0 mm
