IvanCanedo/Re-configurableDrivingSimulatorPrototype/Solidworks/Full-Scale/pin superior.SLDPRT

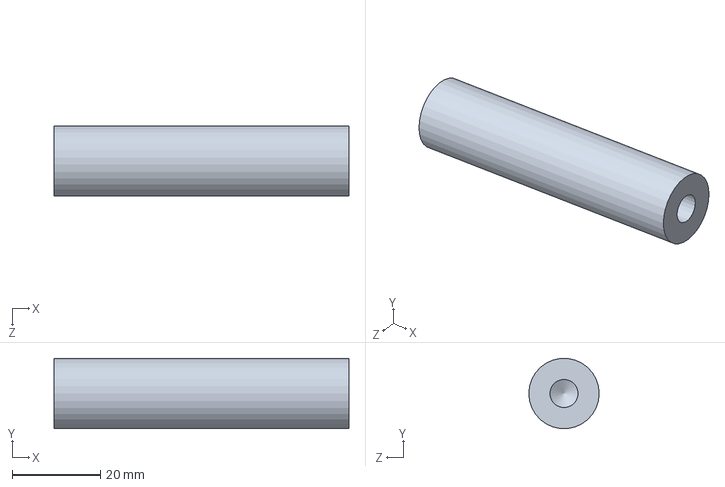
[picture p78: CAD file, 2021-12-05]
Solidworks/Full-Scale/pin superior.SLDPRT
67.0 x 15.9 x 16.0 mm
