IvanCanedo/Re-configurableDrivingSimulatorPrototype/Solidworks/Full-Scale/potenciometro.SLDPRT

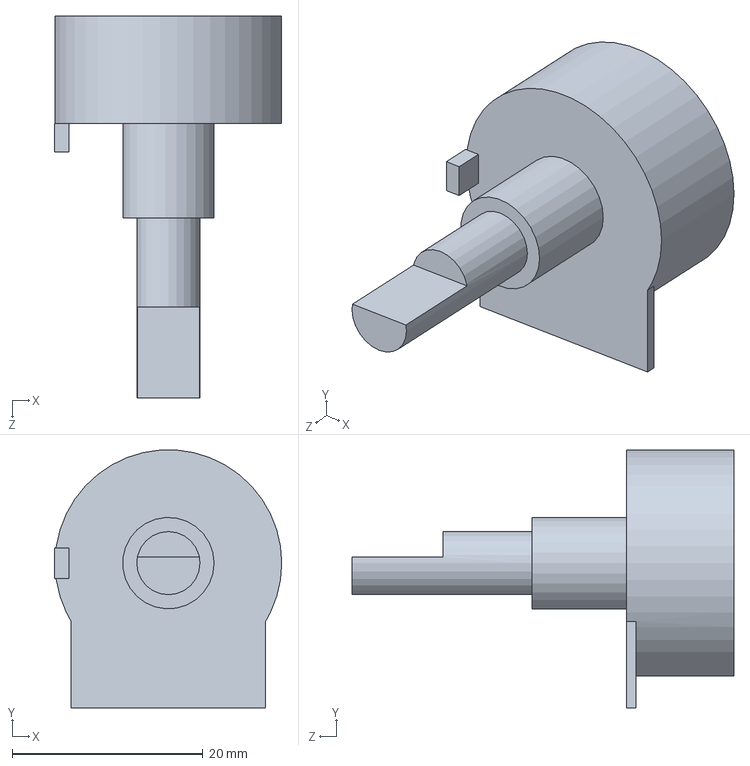
[picture p79: CAD file, 2021-12-05]
Solidworks/Full-Scale/potenciometro.SLDPRT
23.9 x 27.1 x 40.1 mm
