IvanCanedo/Re-configurableDrivingSimulatorPrototype/Solidworks/Full-Scale/virlo superior.SLDPRT

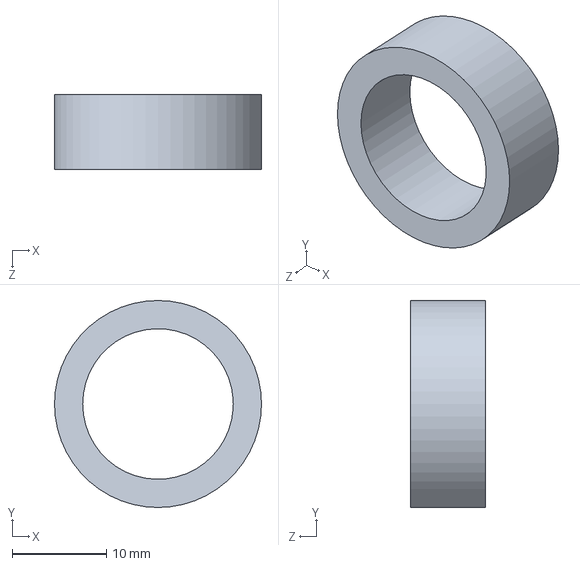
[picture p80: CAD file, 2021-12-05]
Solidworks/Full-Scale/virlo superior.SLDPRT
22.0 x 22.0 x 8.00 mm
