IvanCanedo/Re-configurableDrivingSimulatorPrototype/Solidworks/Full-Scale/arco.SLDPRT

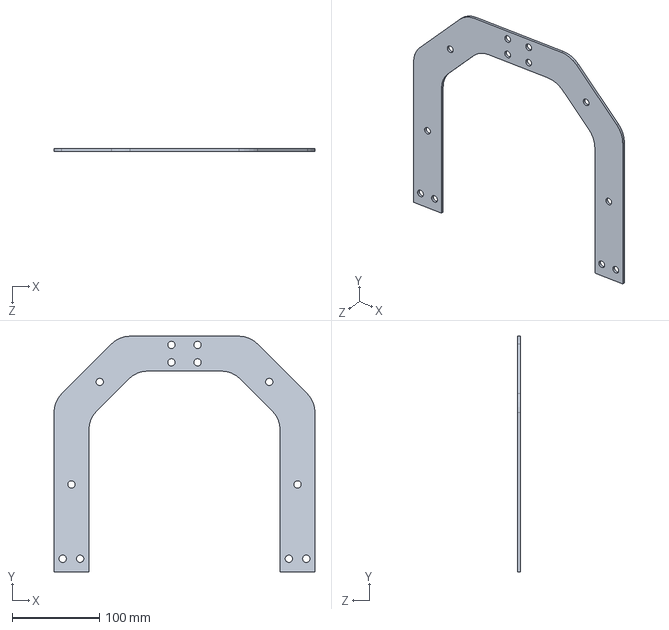
[picture p81: CAD file, 2021-12-05]
Solidworks/Full-Scale/arco.SLDPRT
299.0 x 270.0 x 3.00 mm
