IvanCanedo/Re-configurableDrivingSimulatorPrototype/Solidworks/Full-Scale/base.SLDPRT

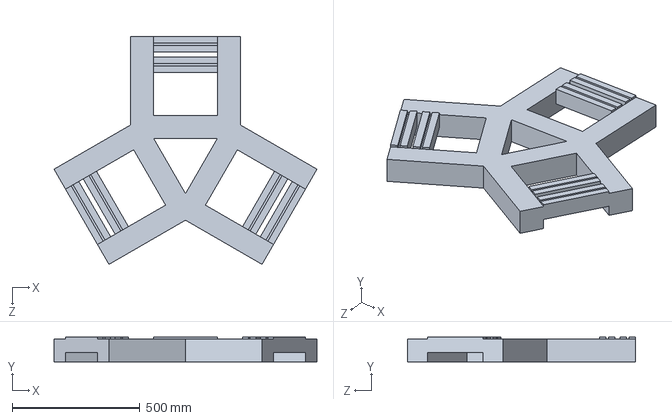
[picture p82: CAD file, 2021-12-05]
Solidworks/Full-Scale/base.SLDPRT
1029.1 x 97.5 x 891.2 mm
